impatrq/green_house/documentacion/historias de usuario/historias_de_usuario.docx

HISTORIAS DE USUARIO

1. Como desarrolladores del proyecto, queremos crear un invernadero inteligente para obtener frutas y verduras fuera de temporada.
2. Como cliente, quiero comprar un sistema que se autocontrole y maneje un historial para cultivar y cosechar frutas y verduras, y tener una mejor dieta.
3. Como agricultor, quiero aumentar mi producción fuera de temporada y utilizar menos agroquímicos para aumentar mis ingresos.
4. Como transportista, quiero tener un fácil manejo para el movimiento del invernadero.
5. Como ONG, quiero fomentar el cultivo en invernadero para reducir el consumo de agua.
6. Como nutricionista, quiero que mis clientes tengan una mejor dieta para tener una mejor calidad de vida.
7. Como encargado de supermercado, quiero tener a la venta frutas y verduras frescas fuera de temporada para satisfacer a mis clientes.
8. Como encargado de vivero, quiero mantener a mis plantas sanas y salvas para venderlas en condiciones.
9. Como escuela, quiero enseñar a mis alumnos la importancia del uso del agua para concientizarlos.
10. Como restaurant, quiero ofrecer a mis clientes la misma calidad/cantidad durante todo el año para evitar la compra de frutas congeladas.
11. Como consorcio de edificio, quiero invernaderos en mi terraza para poder recolectar frutas y verdura de manera conjunta.
