impatrq/green_house/Diseños de marca/Stickers/Instagram.pdf

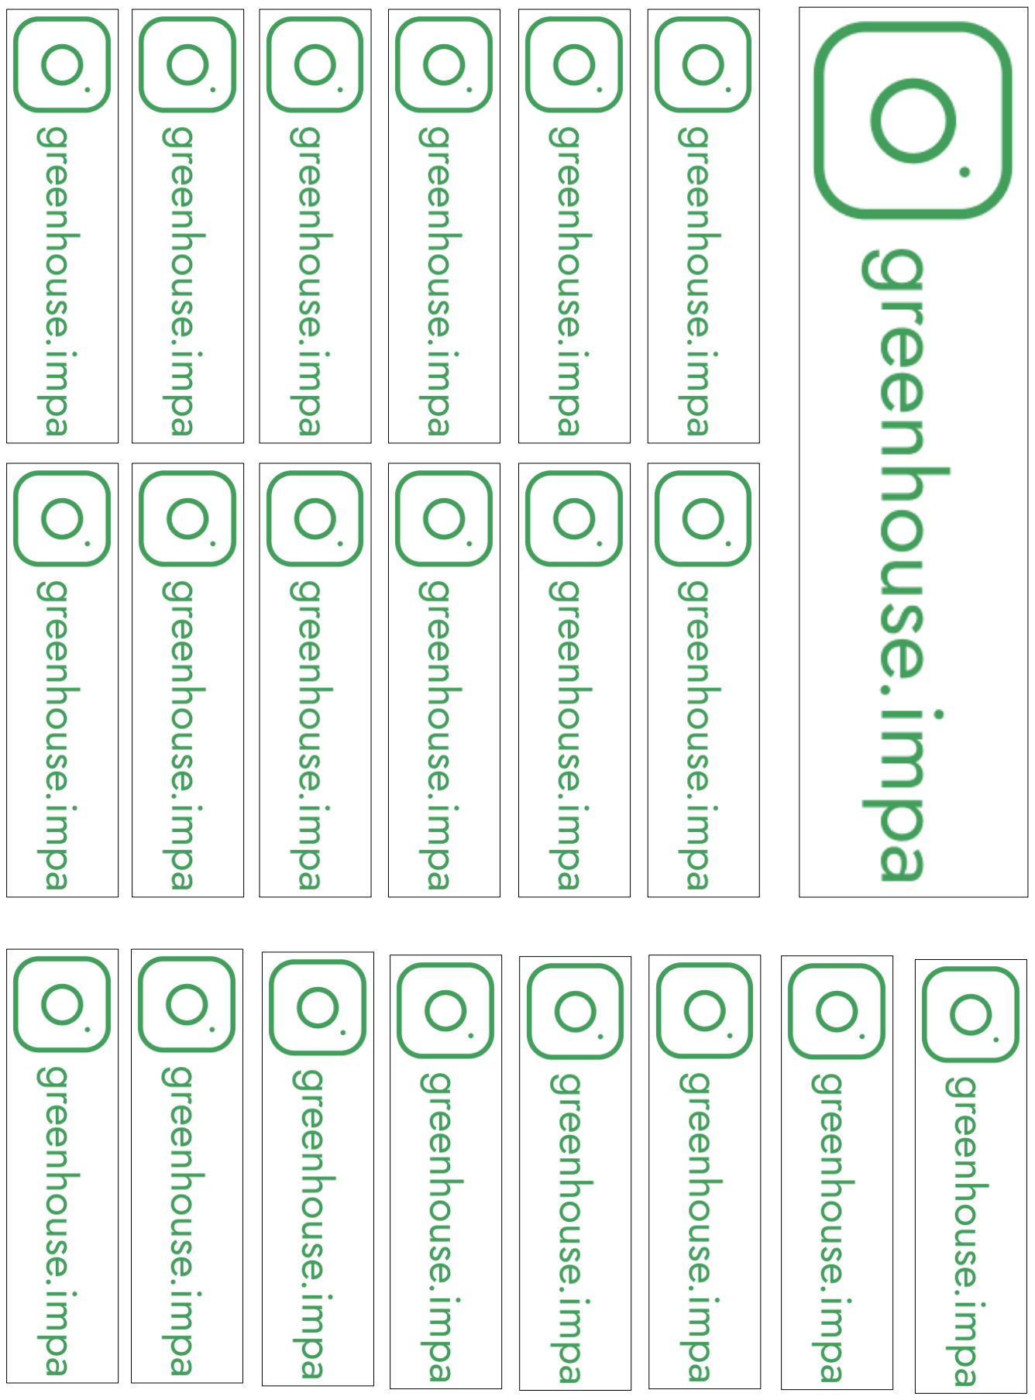
[picture p41: page 1]
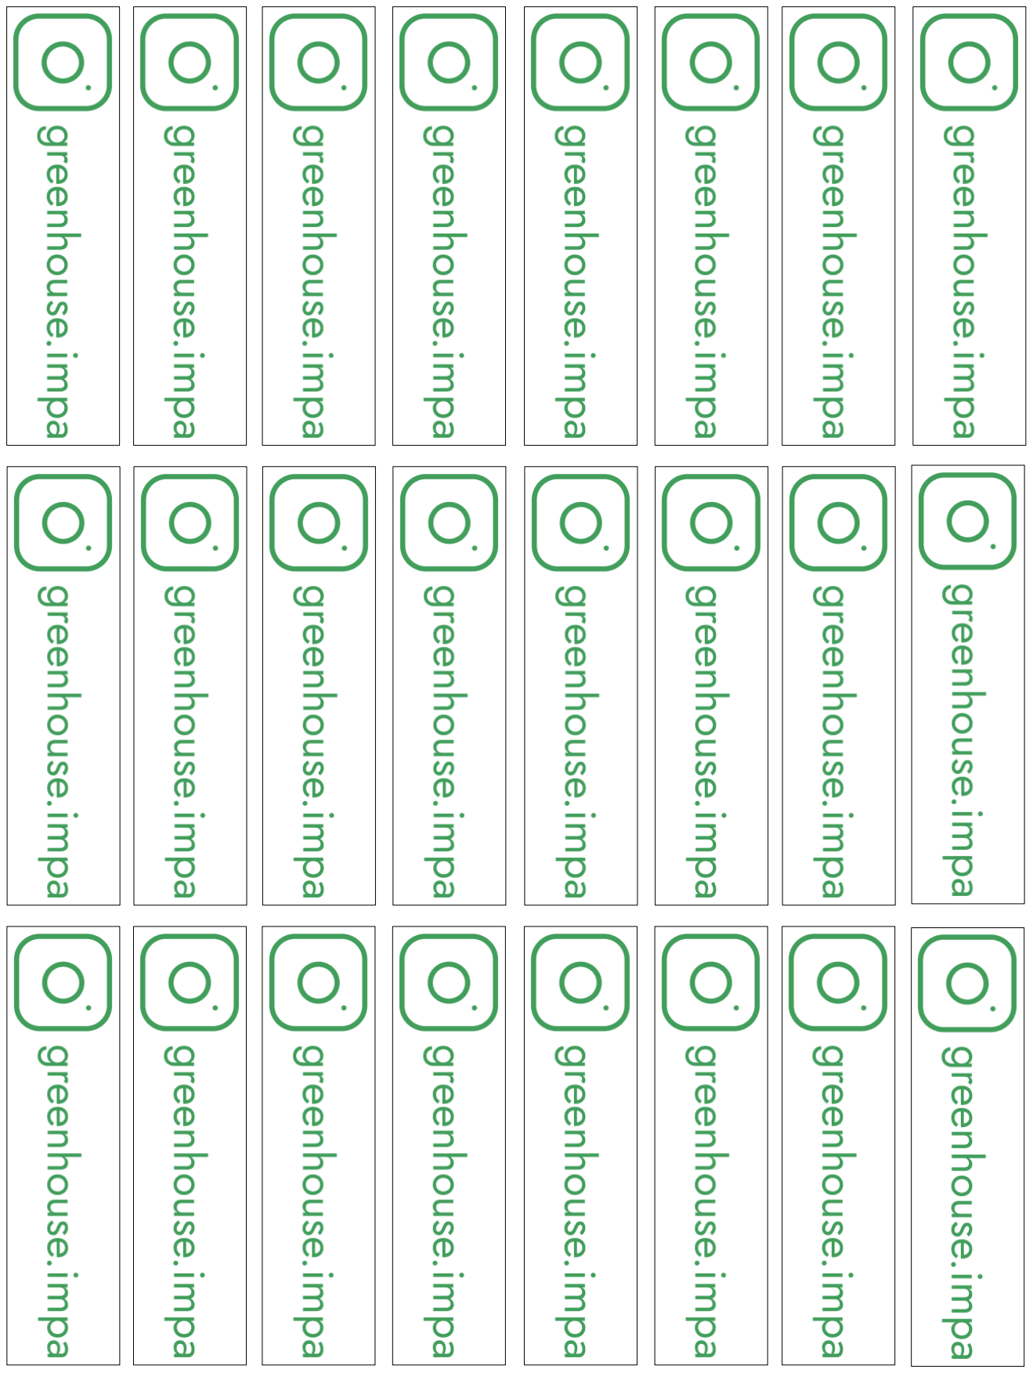
[picture p42: page 2]
