impatrq/green_house/Diseños de marca/Stickers/Nombre y Logo.pdf

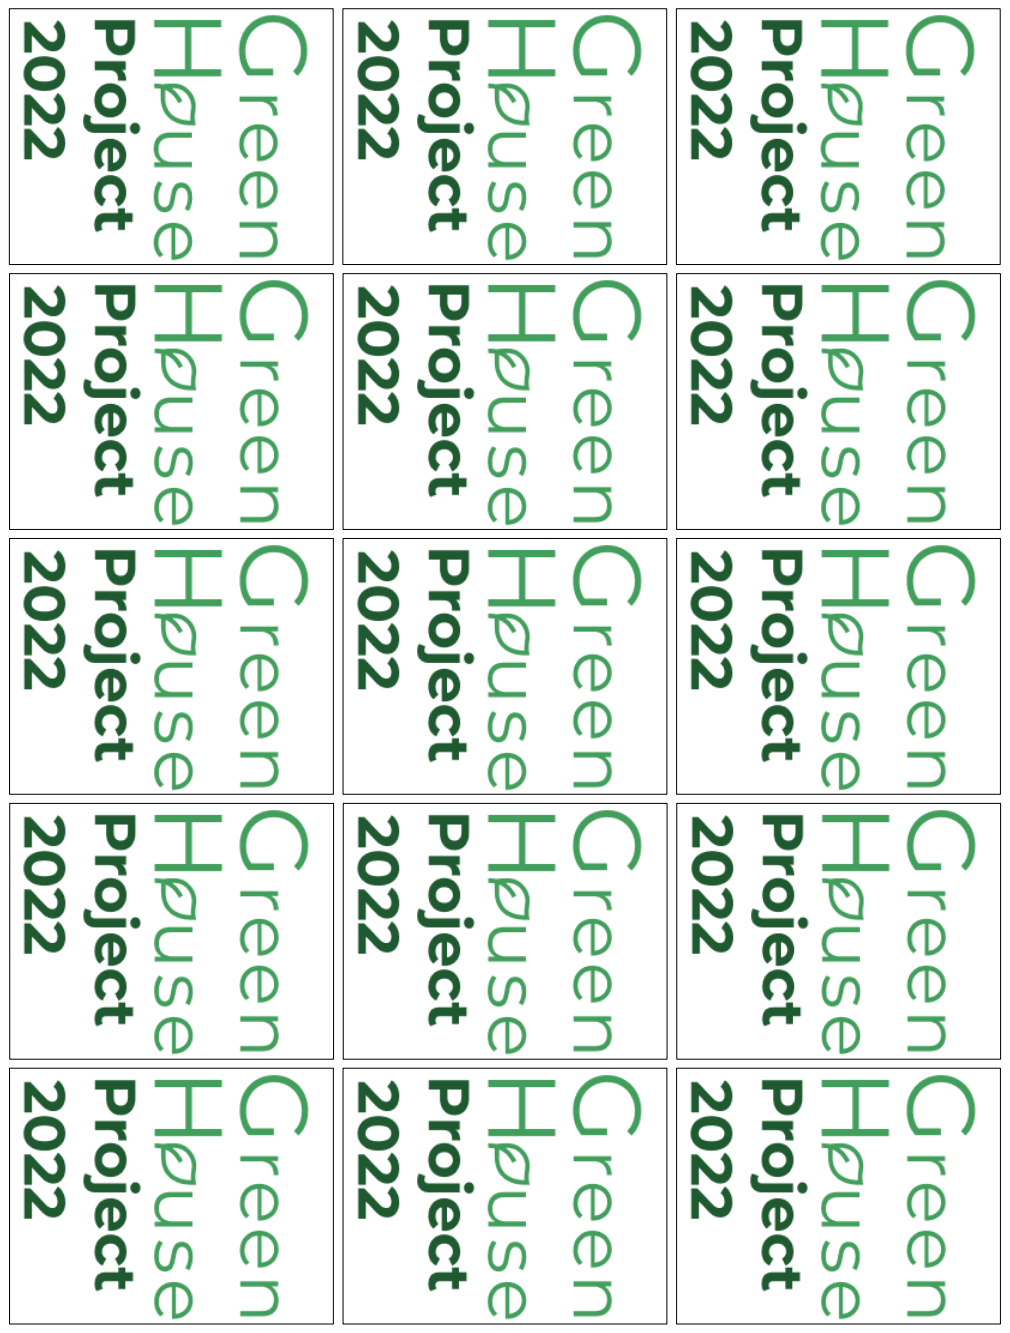
[picture p43: page 1]
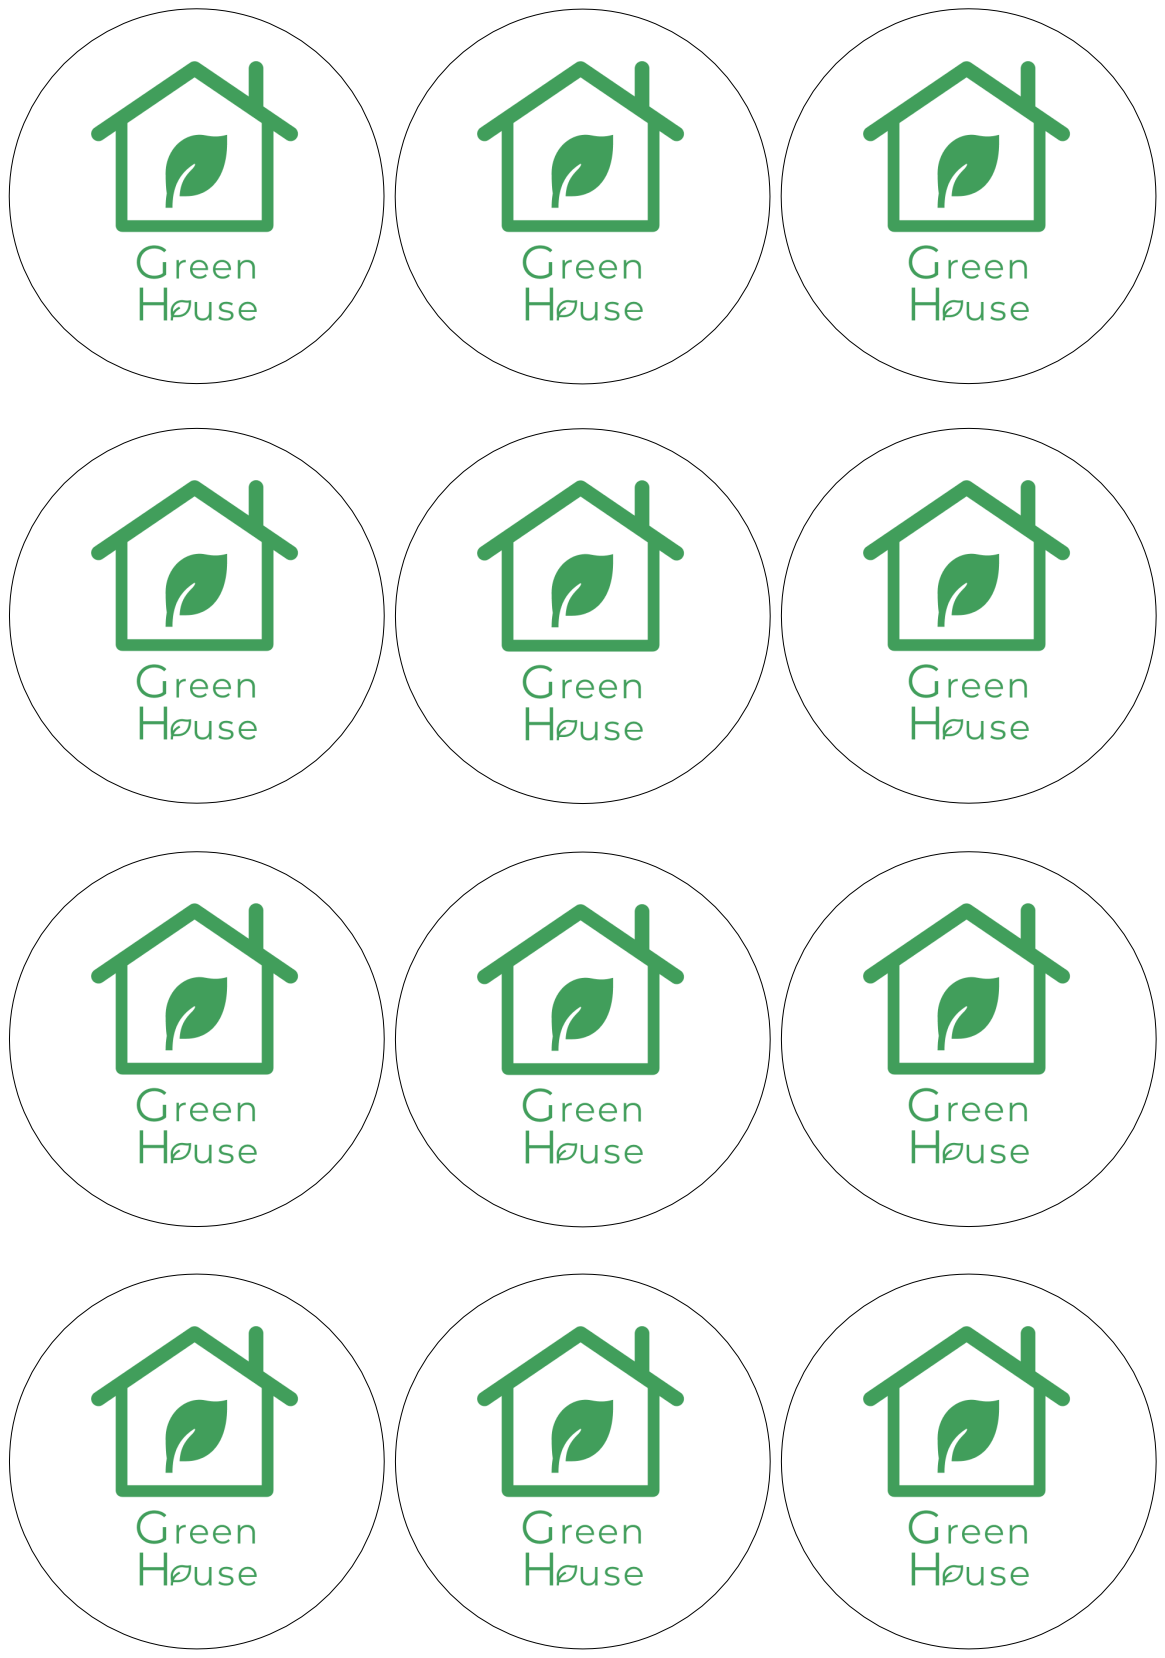
[picture p44: page 3]
