impatrq/green_house/Diseños de marca/Tarjetas de presentacion/Tarjeta de presentacion trasera.pdf

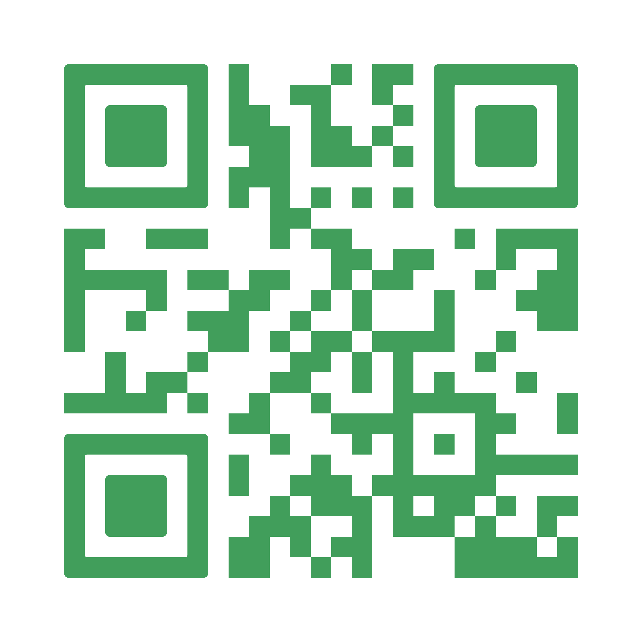
[picture p45: figure]
