impatrq/green_house/documentacion/presentaciones/Presentacion Estilo Venta - GreenHouse.pdf

# ¿Qué es Greenhouse?

GreenHouse es un invernadero automatizado que permite el control de ciertos parámetros como: temperatura y humedad ambiente, luminosidad y humedad de tierra.

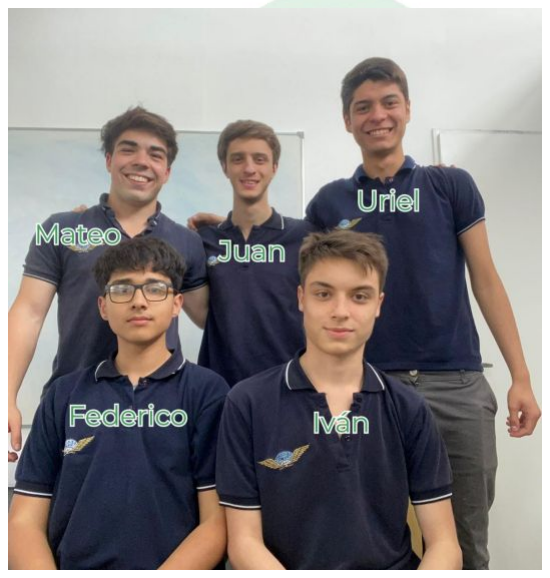
[picture p46: figure]
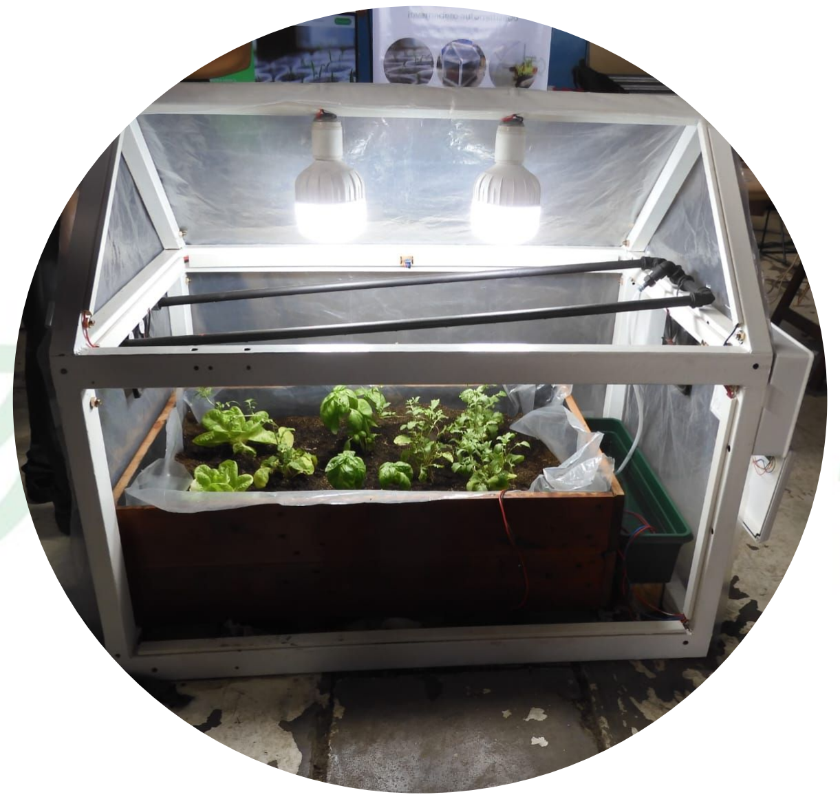
[picture p47: figure]

# ¿A qué apunta Greenhouse?

El objetivo del invernadero es poder darle a nuestros cultivos las condiciones necesarias para desarrollarse, por lo tanto, podemos cultivar plantas que en determinada época no podrían crecer fuera de Greenhouse.
Greenhouse apunta a que cualquier persona que no sepa cómo plantar ni como mantener su cultivo pueda hacerlo sin necesidad de intervenir.

# ¿Por qué adquirir GreenHouse?

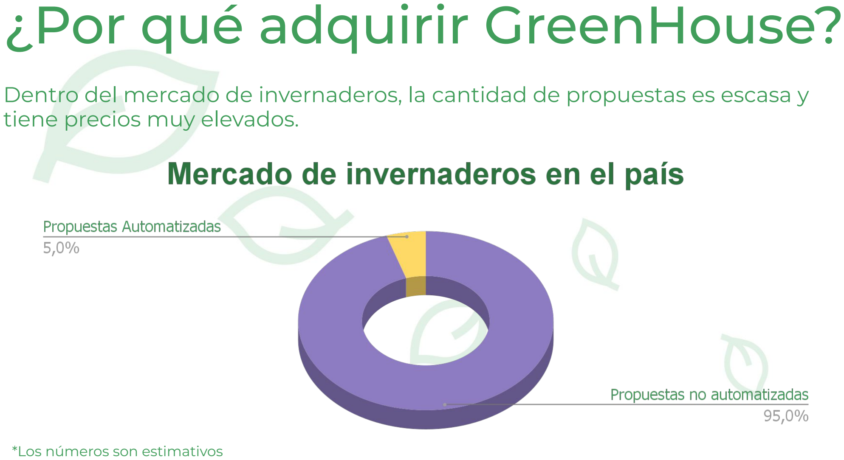
[picture p48: page 4]

Dentro del mercado de invernaderos, la cantidad de propuestas es escasa y tiene precios muy elevados.

*Los números son estimativos

## ¿Podría GreenHouse ingresar al mercado?

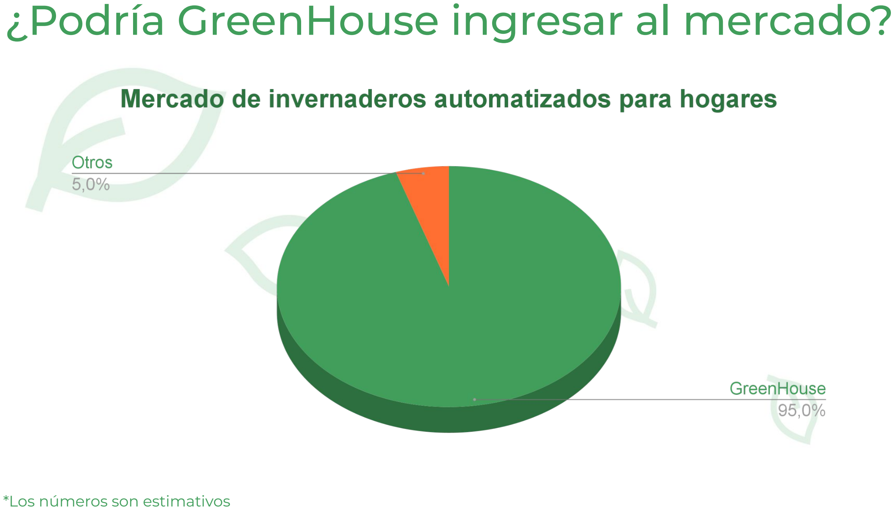
[picture p49: page 5]

*Los números son estimativos

# Ventajas frente a la competencia

### Total automatización

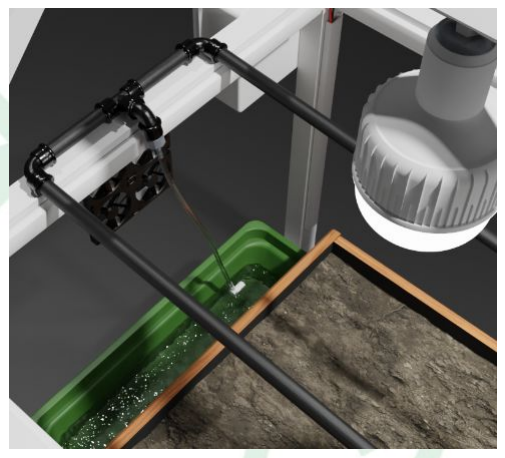
[picture p50: figure]
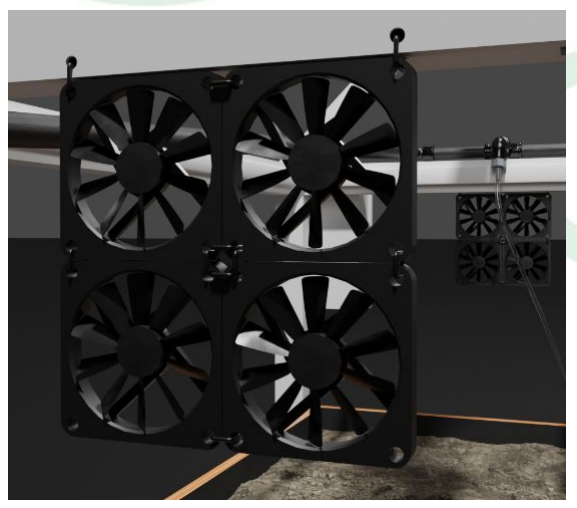
[picture p51: figure]
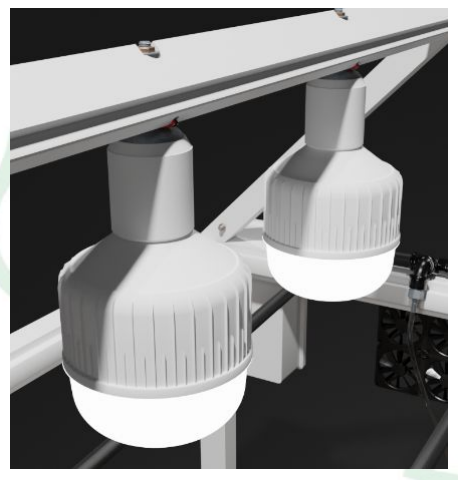
[picture p52: figure]

# Ventajas frente a la competencia

## Interfaz personalizada

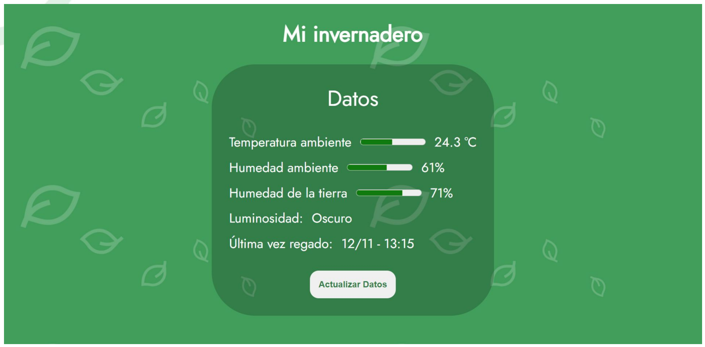
[picture p53: figure]

# Ventajas frente a la competencia

## Relación costo - calidad inmejorable

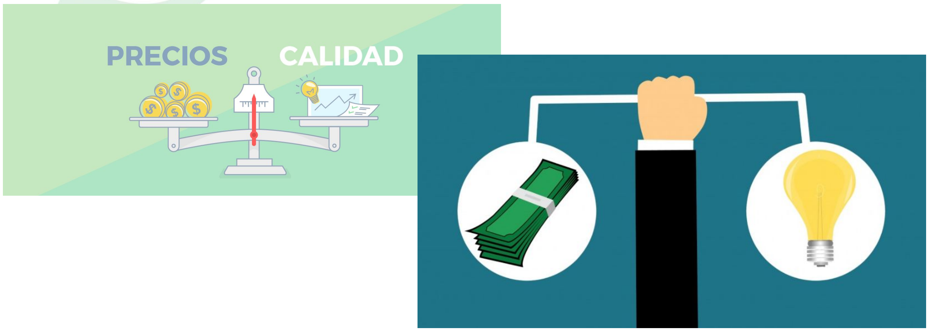
[picture p54: figure]

# Estructura

## Diseño de los planos

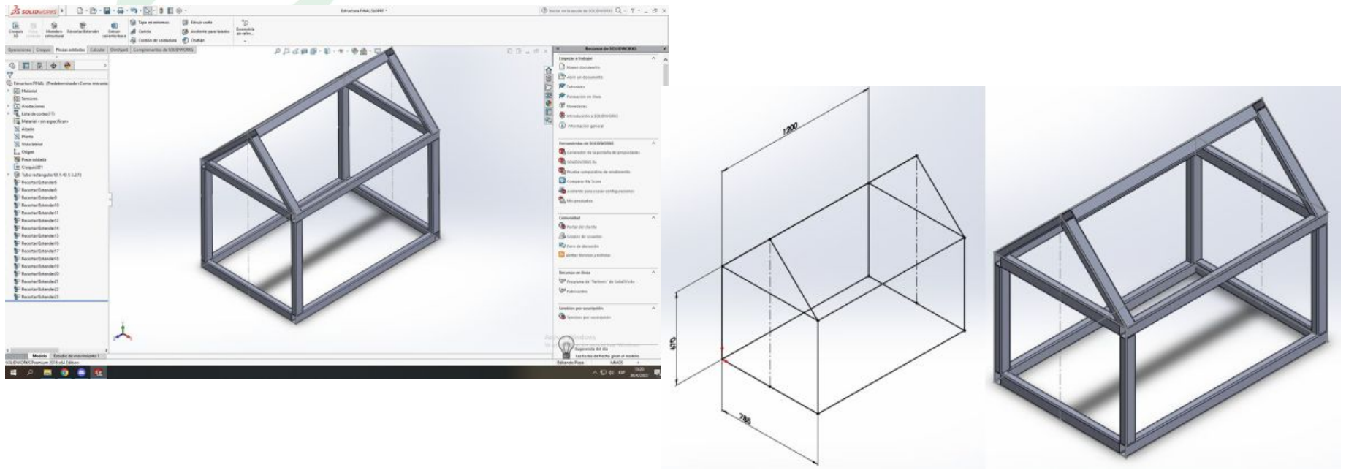
[picture p55: figure]

# Estructura

## Desarrollo

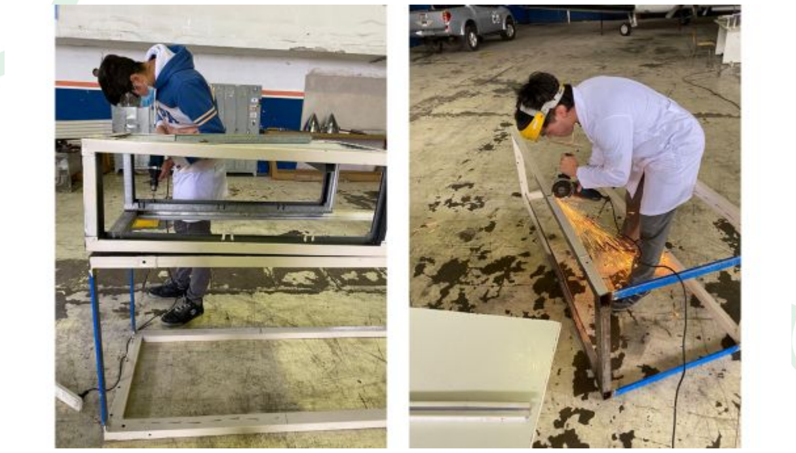
[picture p56: figure]

# Estructura

## Desarrollo

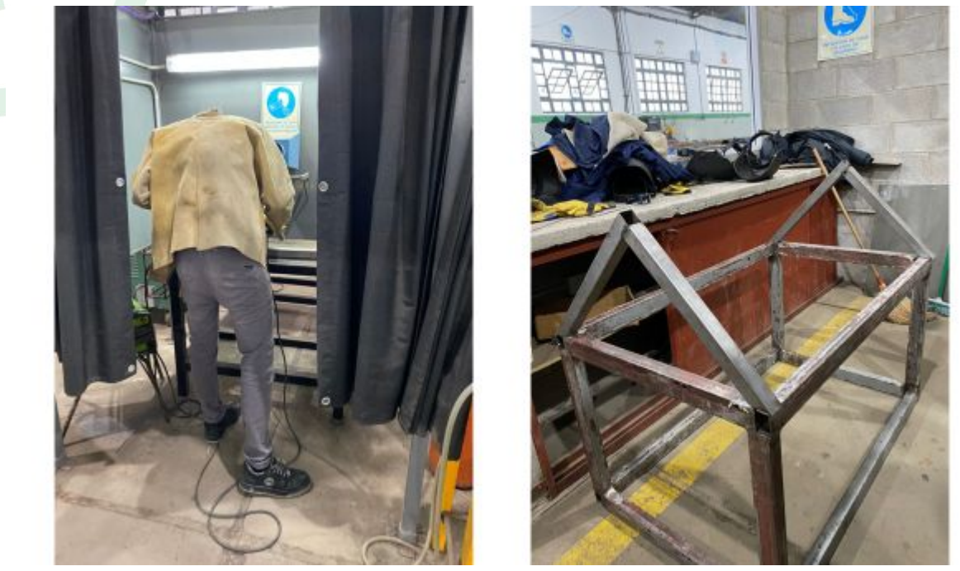
[picture p57: figure]

# Estructura

## Desarrollo

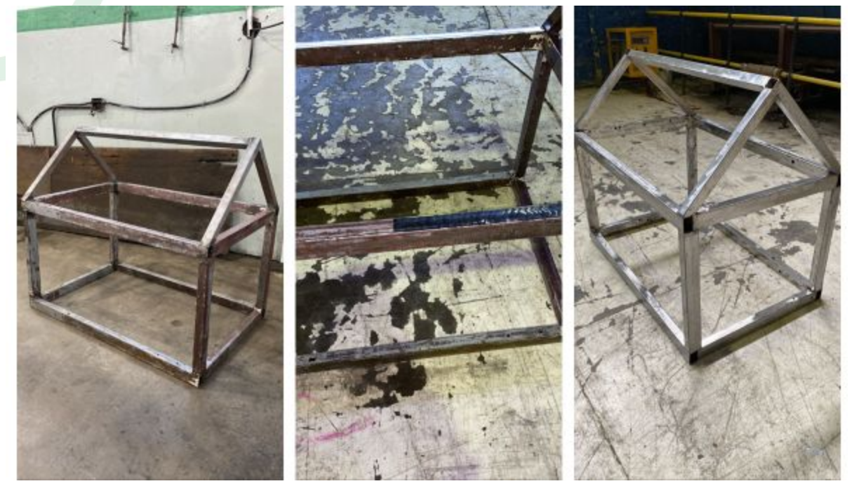
[picture p58: figure]

# Estructura del cajón

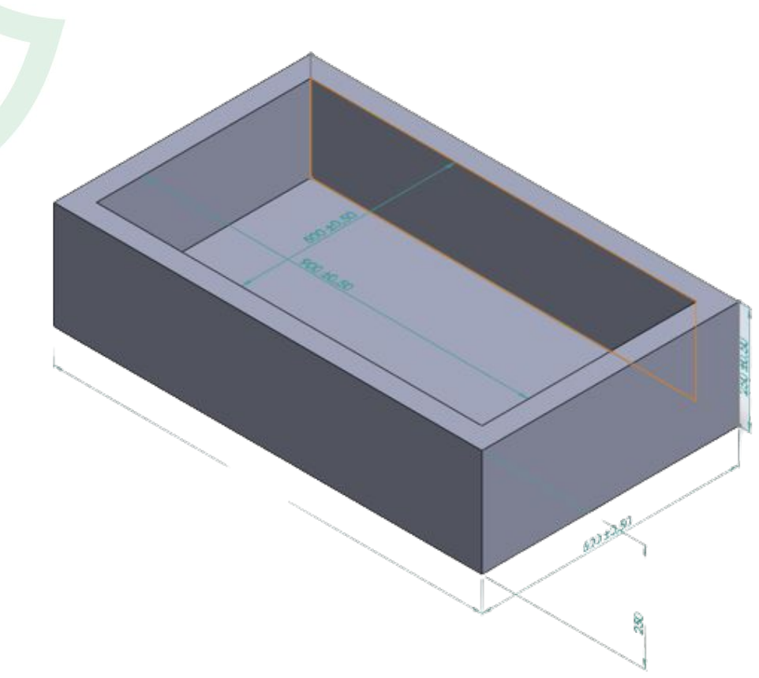
[picture p59: figure]

## Diseño

# Estructura del cajón

## Desarrollo

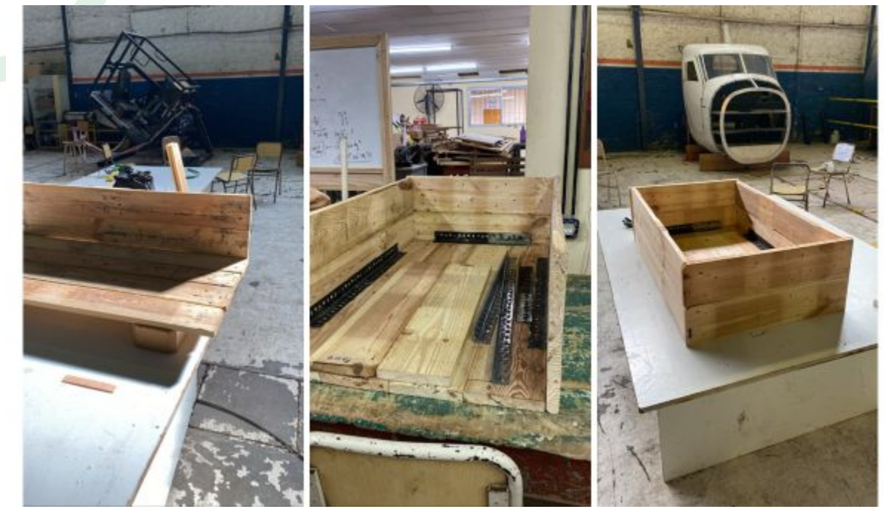
[picture p60: figure]

# Circuito electrónico

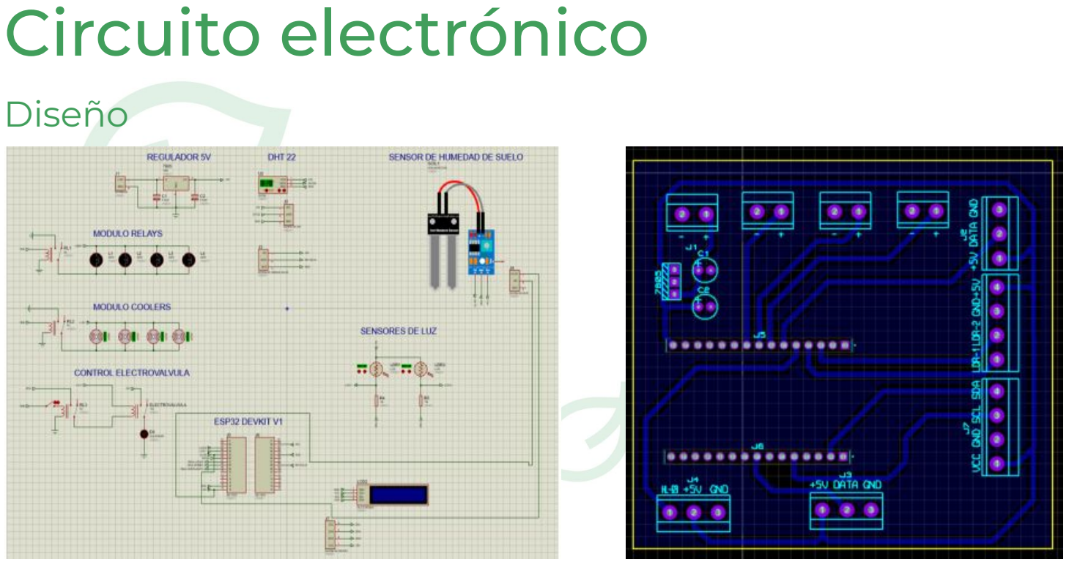
[picture p61: page 15]

Diseño

# Circuito electrónico

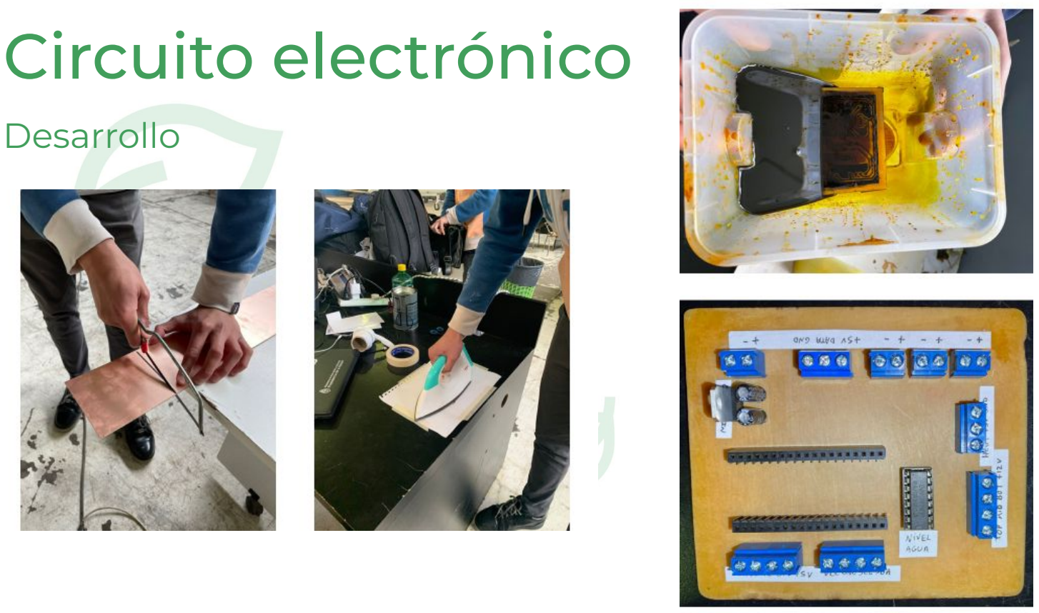
[picture p62: page 16]

Desarrollo

# Funcionamiento de hardware

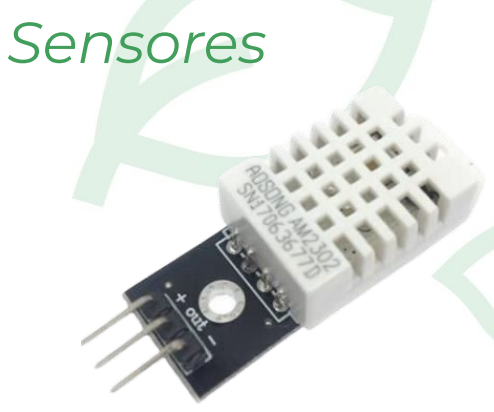
[picture p63: figure]
Sensores
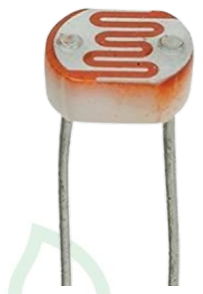
[picture p64: figure]
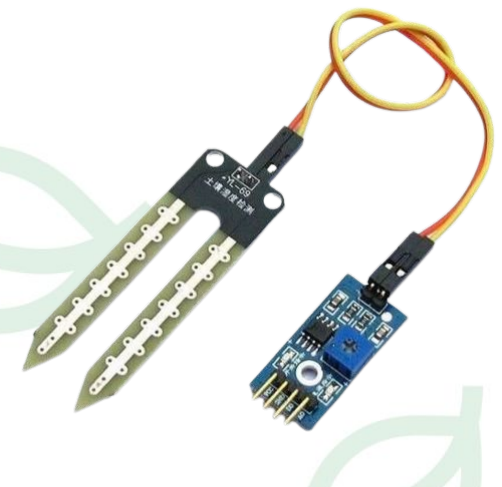
[picture p65: figure]
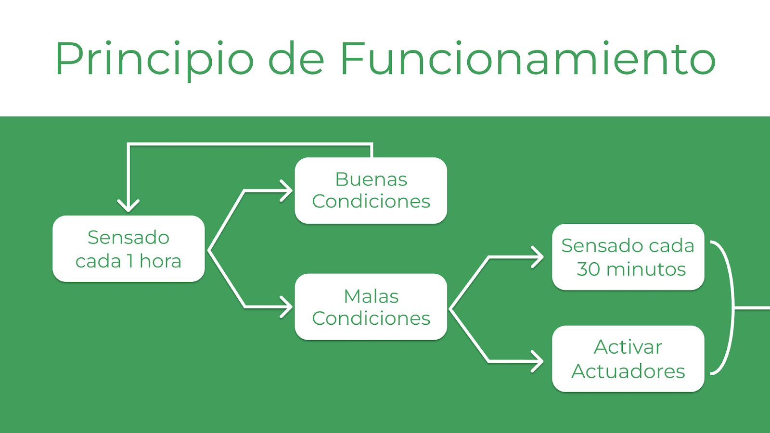
[picture p66: page 18]
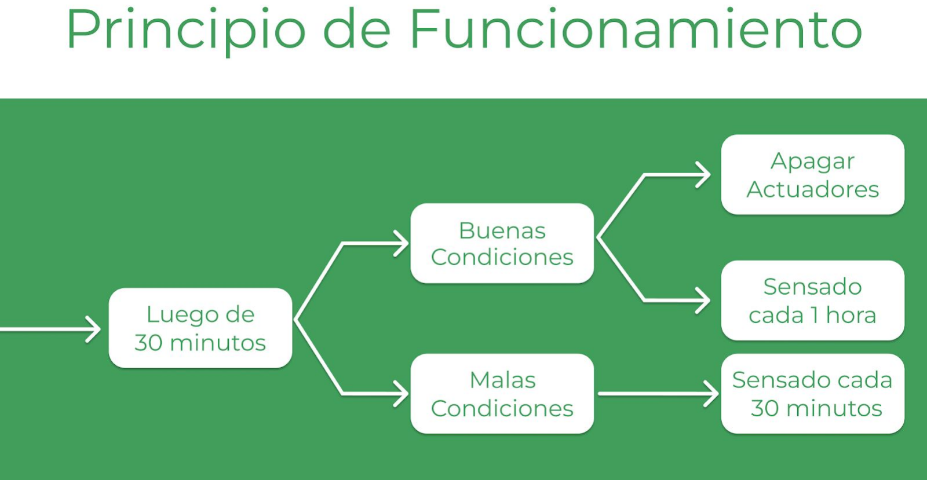
[picture p67: page 19]

# Diseño 3D

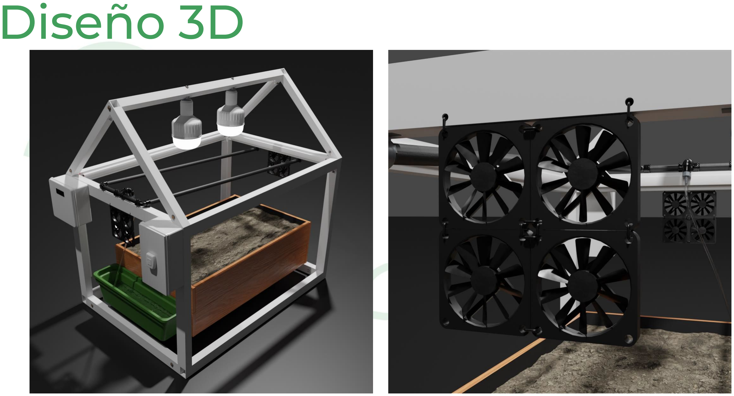
[picture p68: page 20]

# Diseño 3D

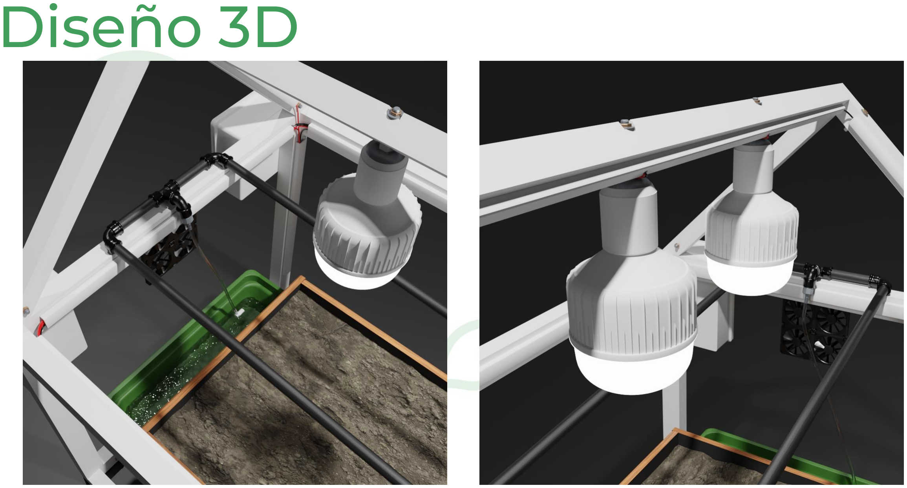
[picture p69: page 21]

# Diseño 3D

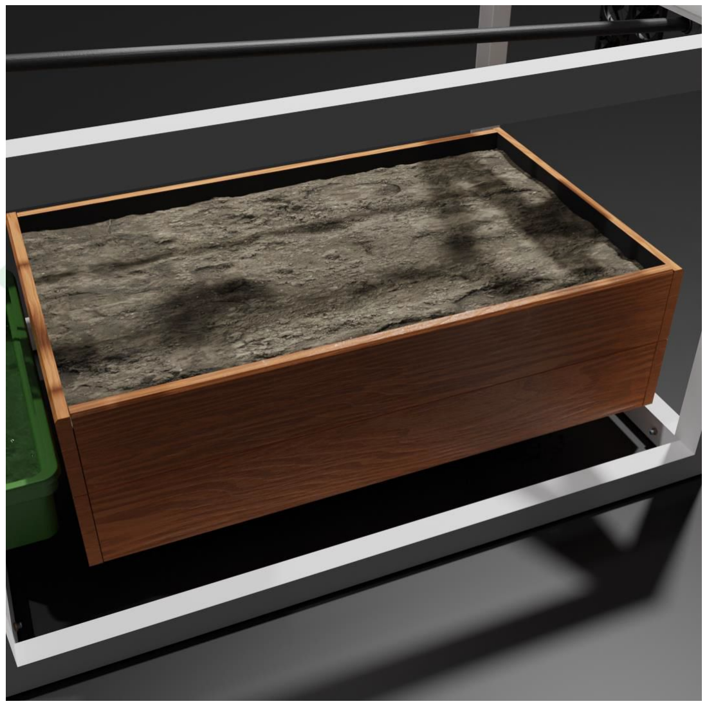
[picture p70: figure]

# Página web

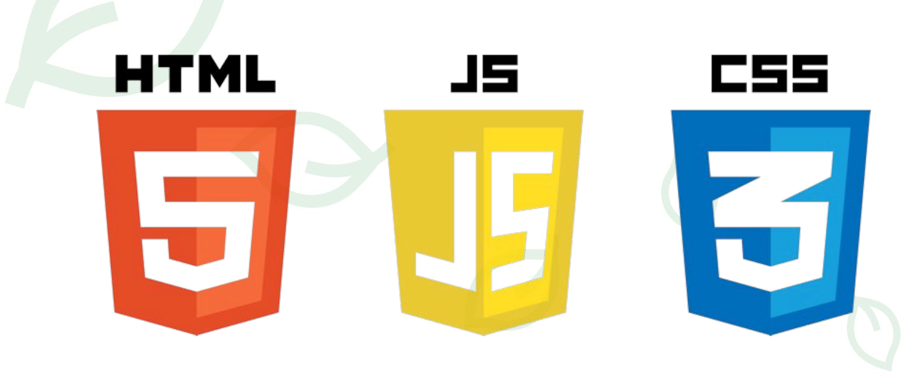
[picture p71: figure]

# Página web

Desarrollo

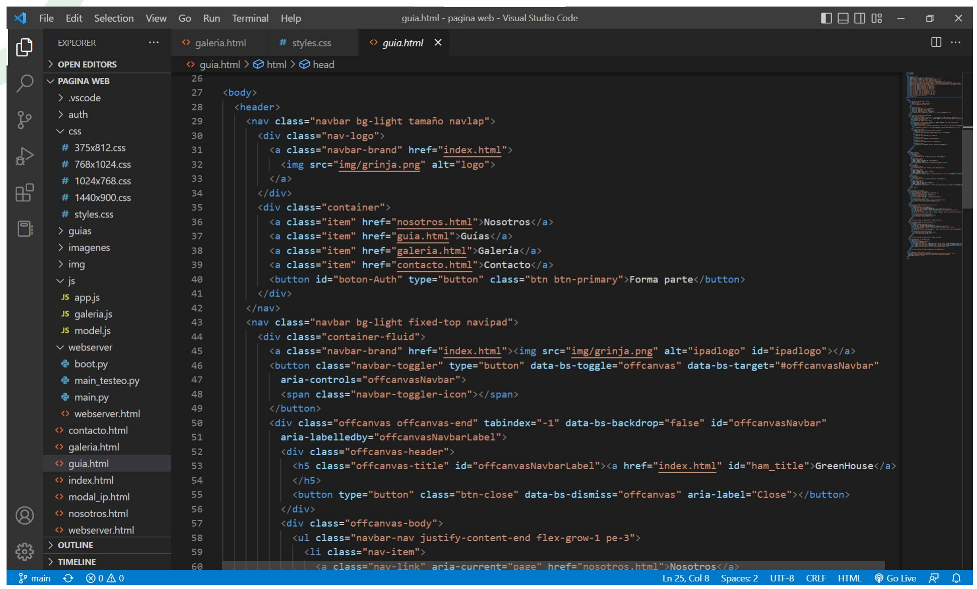
[picture p72: figure]

# Página web

Resultado

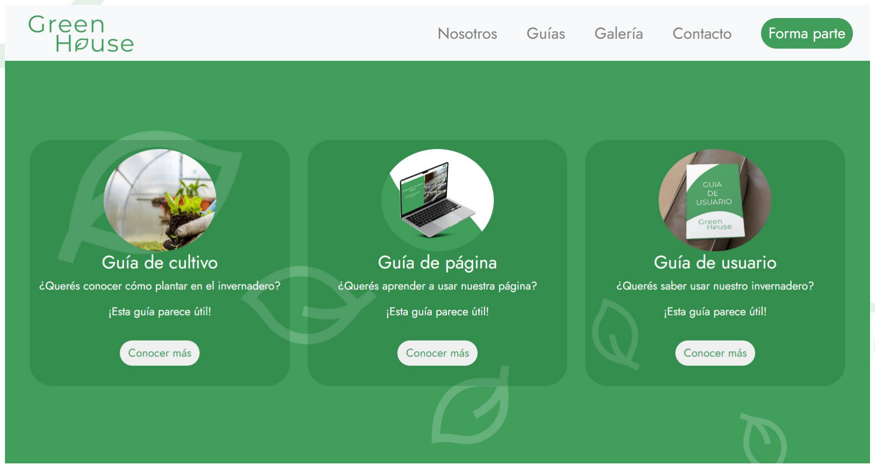
[picture p73: figure]
