impatrq/green_house/pagina web/img/Background_Guias.png

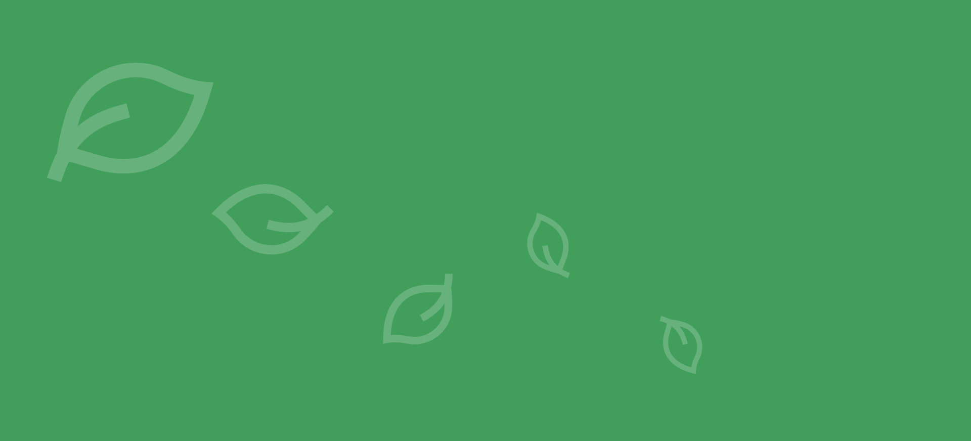
pagina web/img/Background_Guias.png
