impatrq/green_house/pagina web/img/fede.png

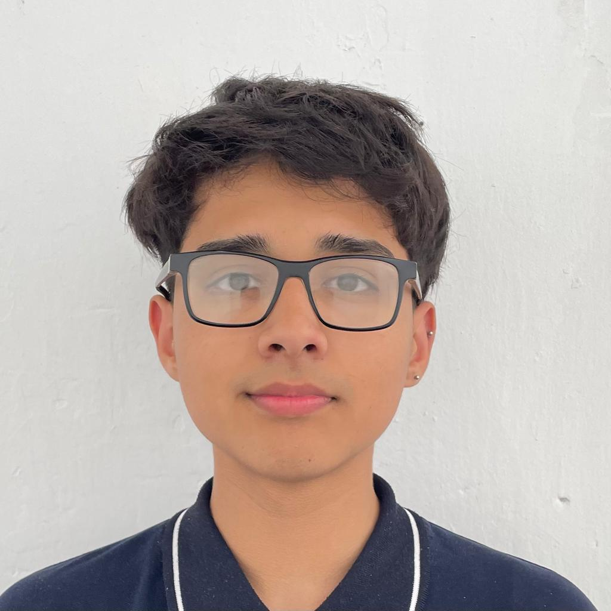
pagina web/img/fede.png
