impatrq/green_house/pagina web/img/grinja.png

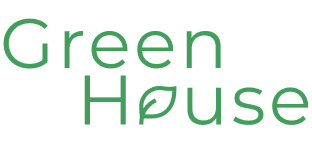
pagina web/img/grinja.png
