impatrq/green_house/pagina web/img/guia_pagina.png

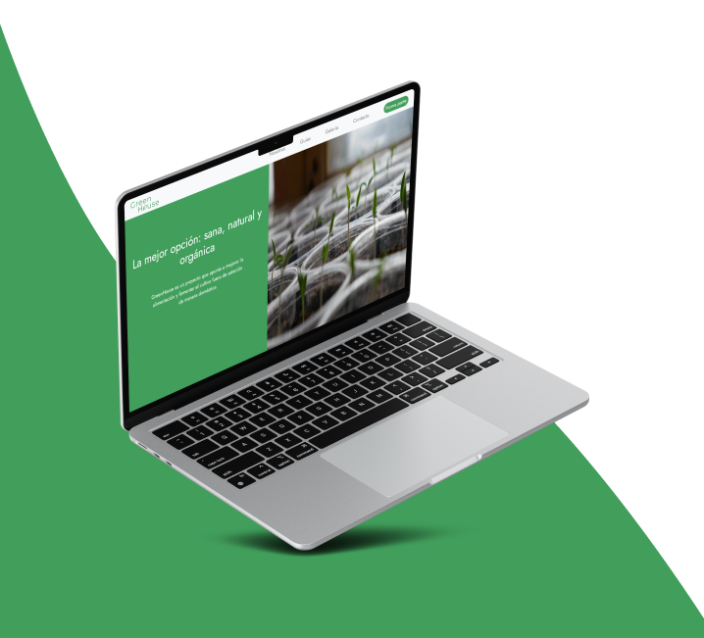
pagina web/img/guia_pagina.png
