impatrq/green_house/pagina web/img/ivan.jpg

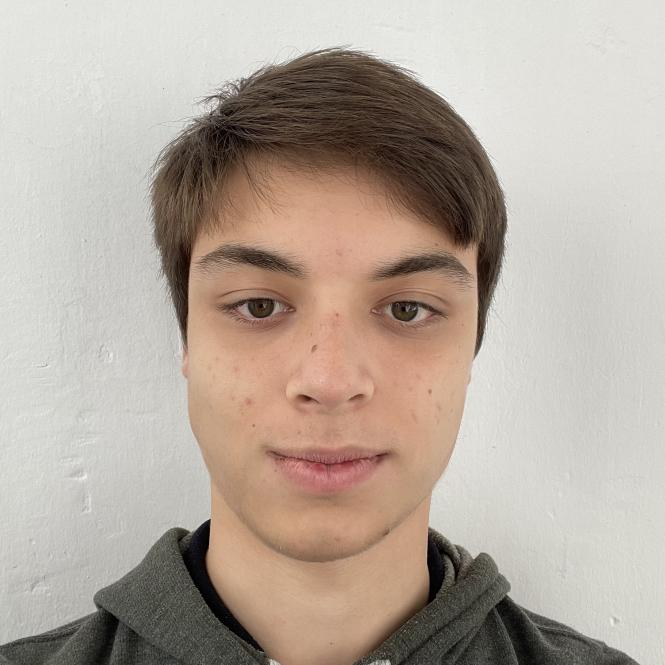
pagina web/img/ivan.jpg
