impatrq/green_house/pagina web/img/juan.jpg

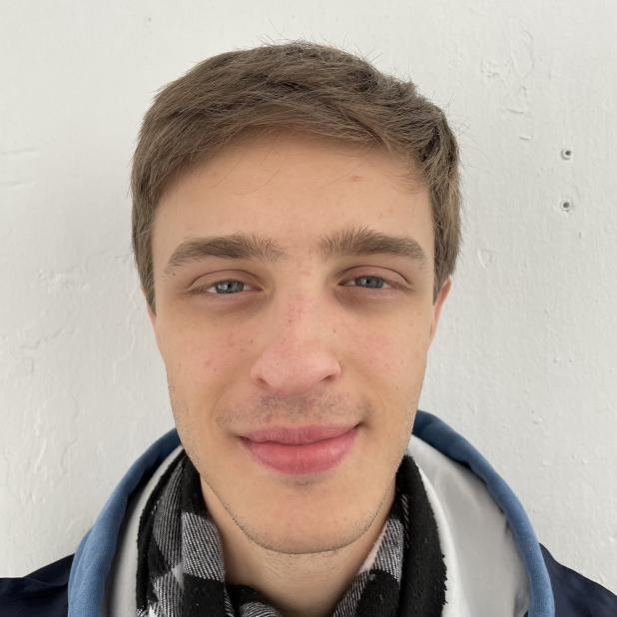
pagina web/img/juan.jpg
