impatrq/green_house/pagina web/img/mateo.jpg

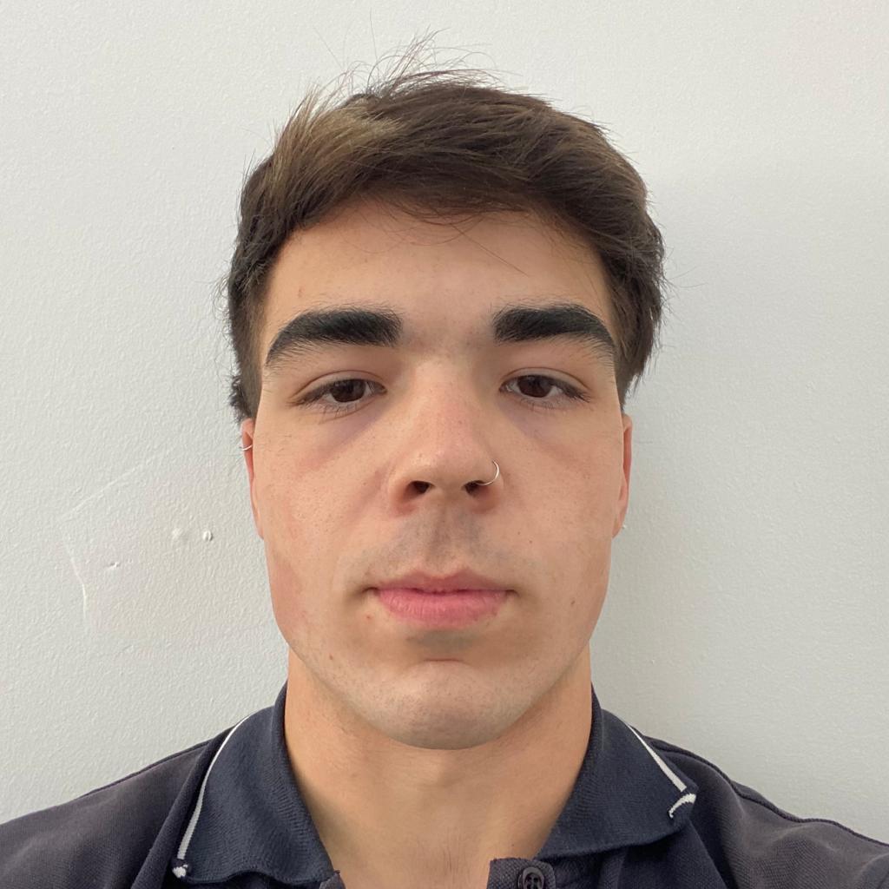
pagina web/img/mateo.jpg
