impatrq/green_house/pagina web/img/momo.PNG

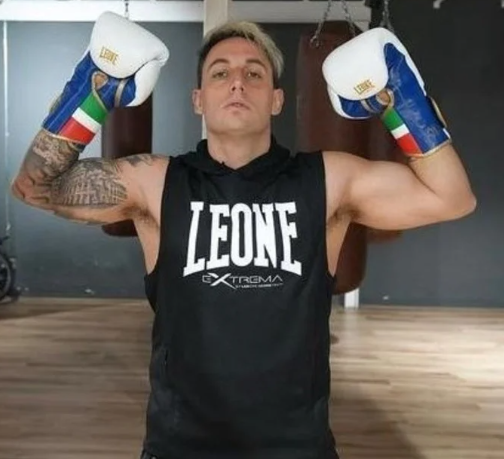
pagina web/img/momo.PNG
