impatrq/green_house/pagina web/img/proceso 1.jpeg

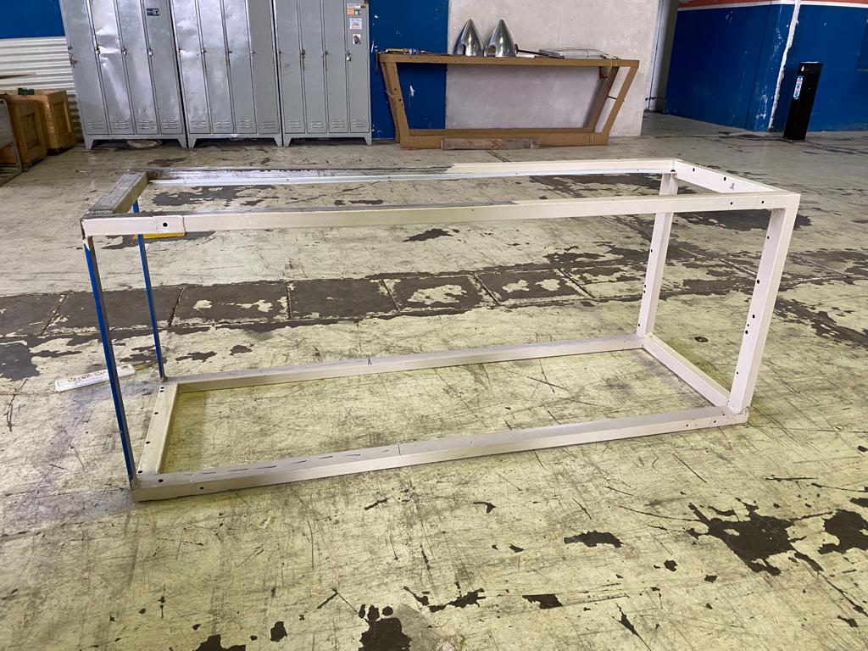
pagina web/img/proceso 1.jpeg
