impatrq/green_house/pagina web/img/proceso 2.jpeg

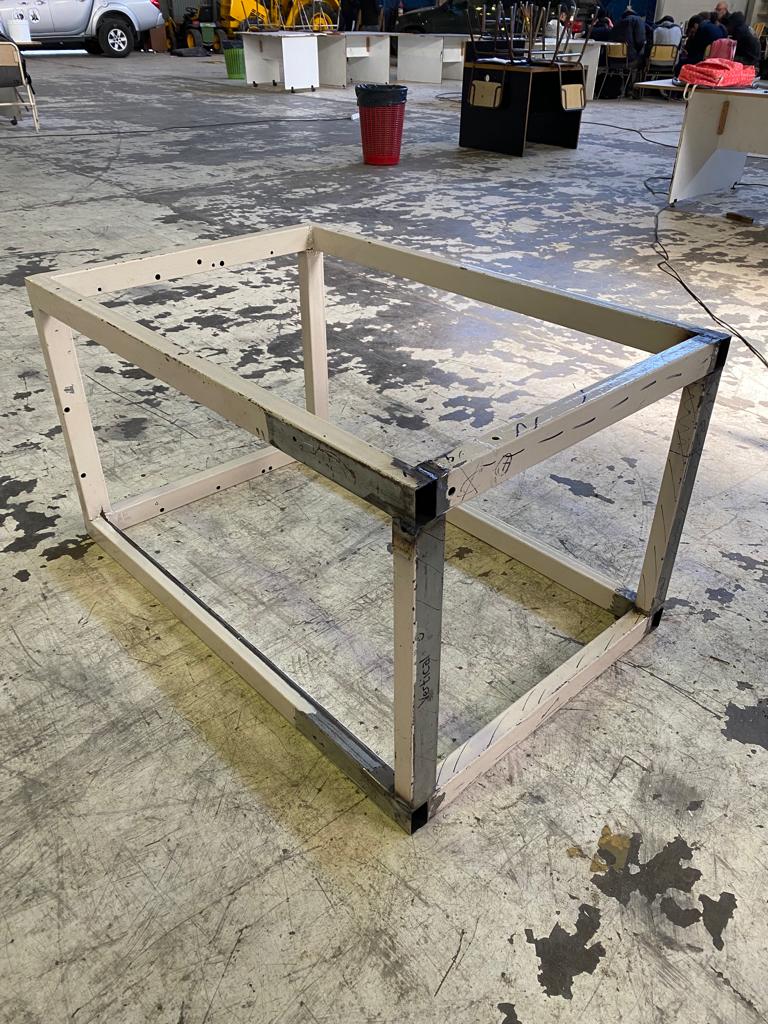
pagina web/img/proceso 2.jpeg
