impatrq/green_house/pagina web/img/proceso 3.jpeg

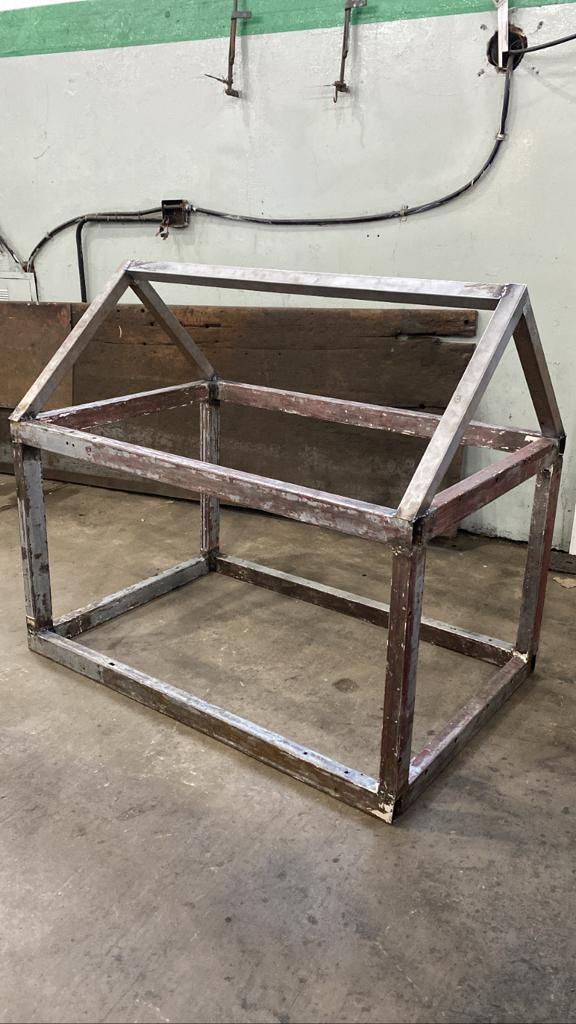
pagina web/img/proceso 3.jpeg
