impatrq/green_house/pagina web/img/proceso 4.jpeg

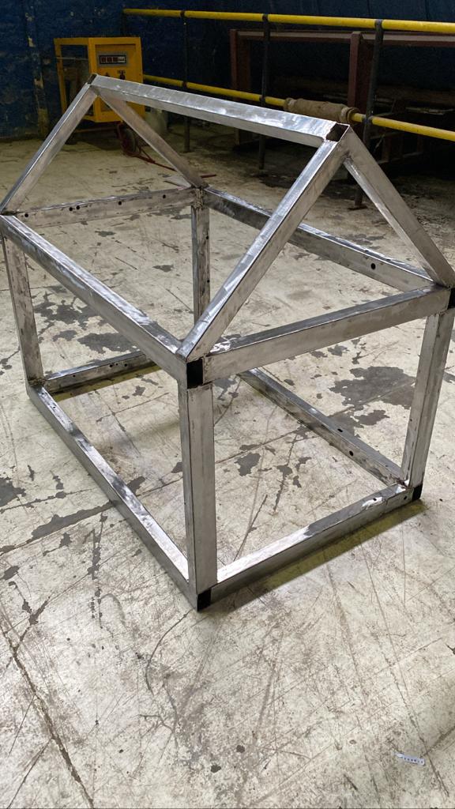
pagina web/img/proceso 4.jpeg
