impatrq/green_house/pagina web/img/proceso 5.jpeg

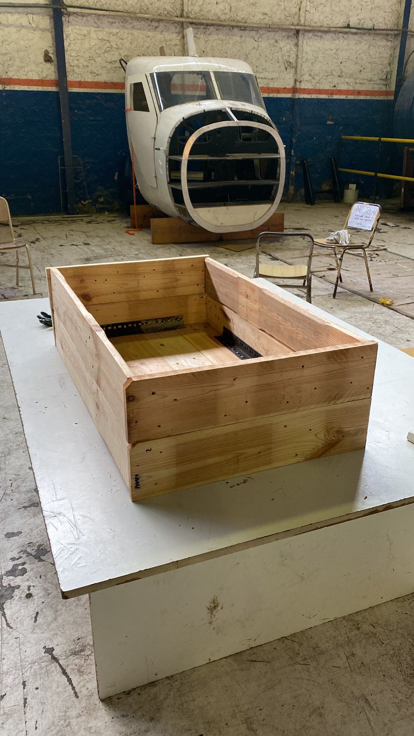
pagina web/img/proceso 5.jpeg
