impatrq/green_house/pagina web/img/proceso 6.jpeg

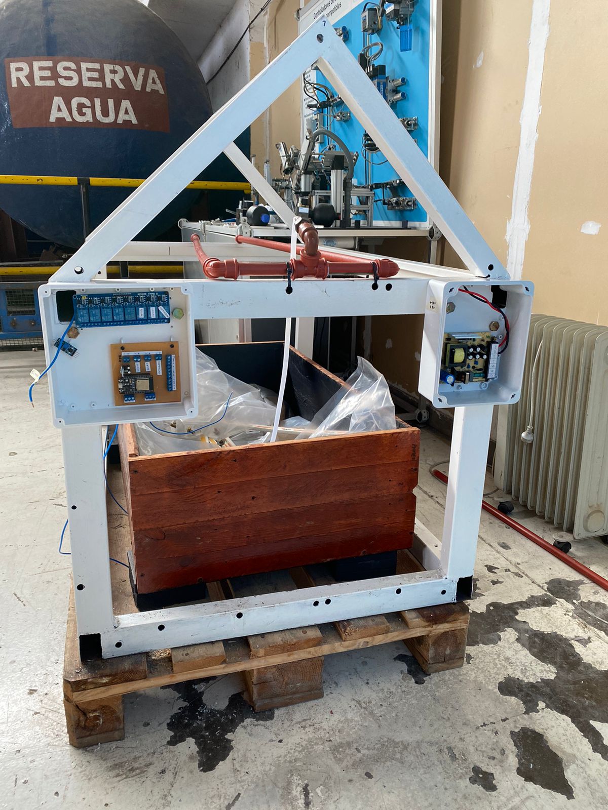
pagina web/img/proceso 6.jpeg
