impatrq/green_house/pagina web/img/proceso 7.jpeg

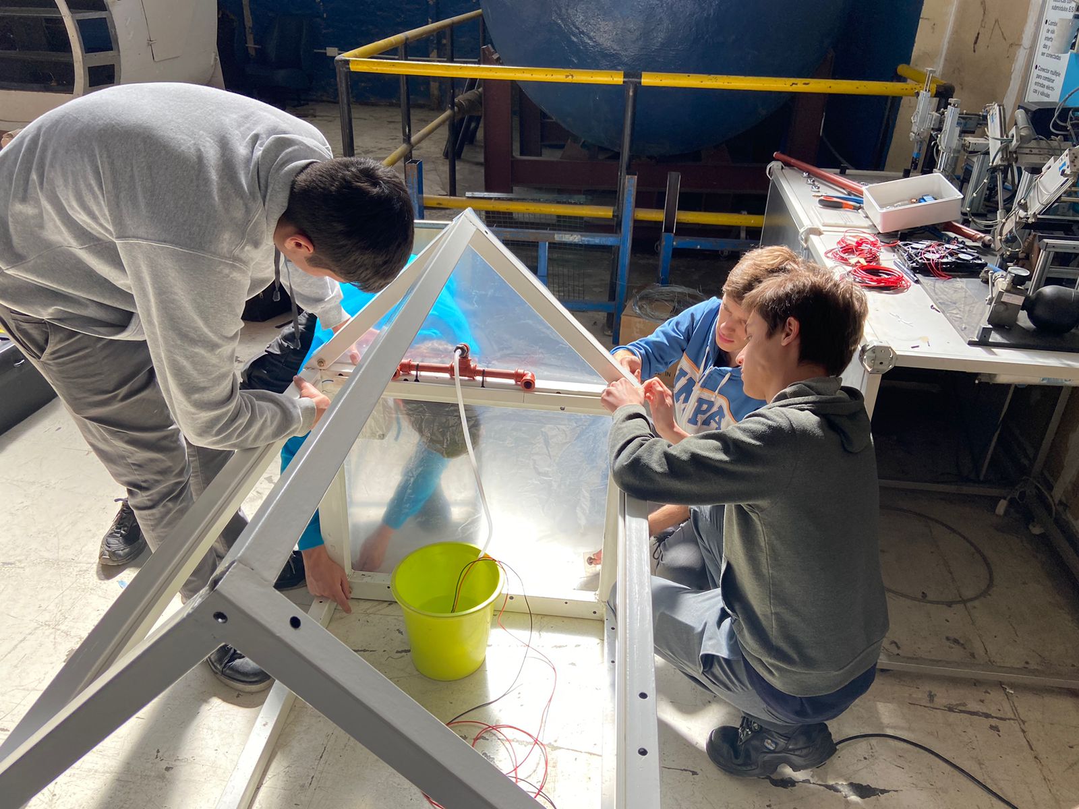
pagina web/img/proceso 7.jpeg
