impatrq/green_house/pagina web/img/proceso 8.jpeg

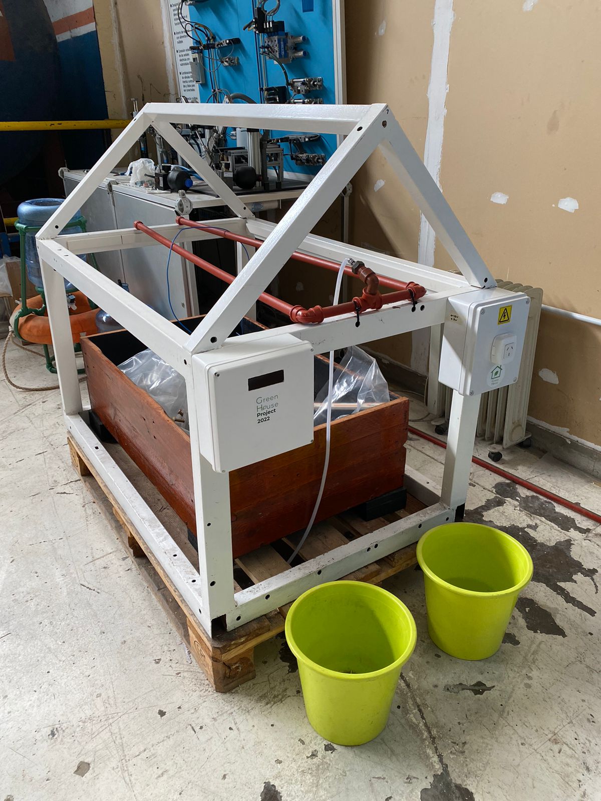
pagina web/img/proceso 8.jpeg
