impatrq/green_house/pagina web/img/proceso 9.jpg

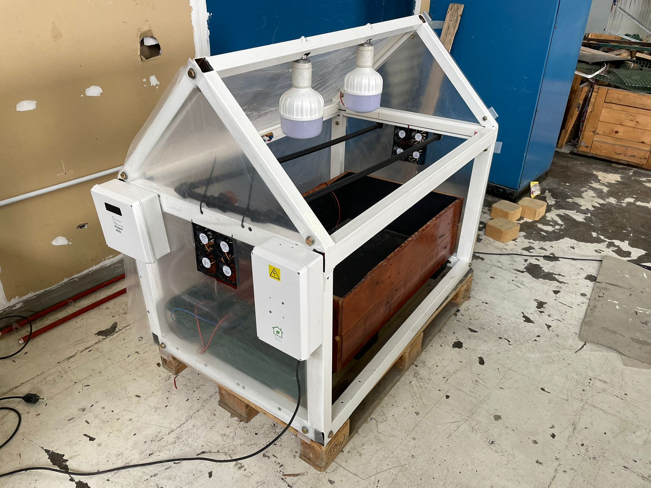
pagina web/img/proceso 9.jpg
