impatrq/green_house/pagina web/img/uriel.jpg

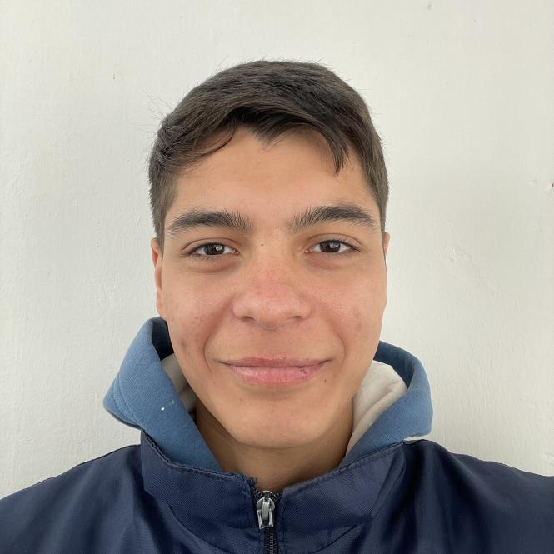
pagina web/img/uriel.jpg
