impatrq/green_house/Proteus/Esquematico.png

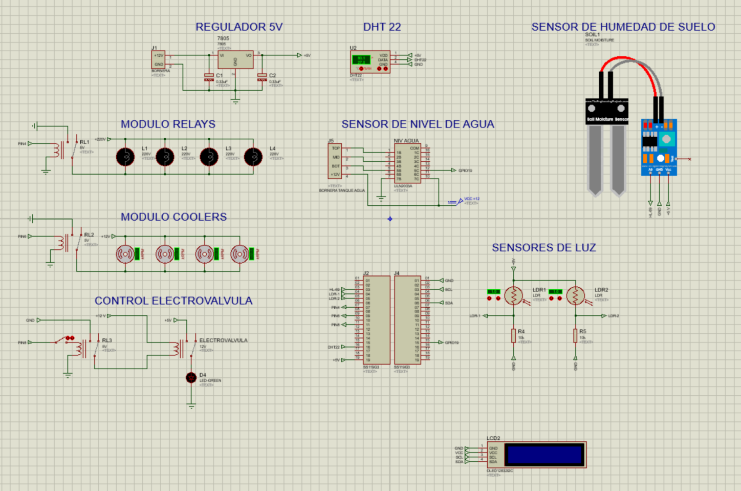
Proteus/Esquematico.png
