impatrq/green_house/Proteus/PCB layout.png

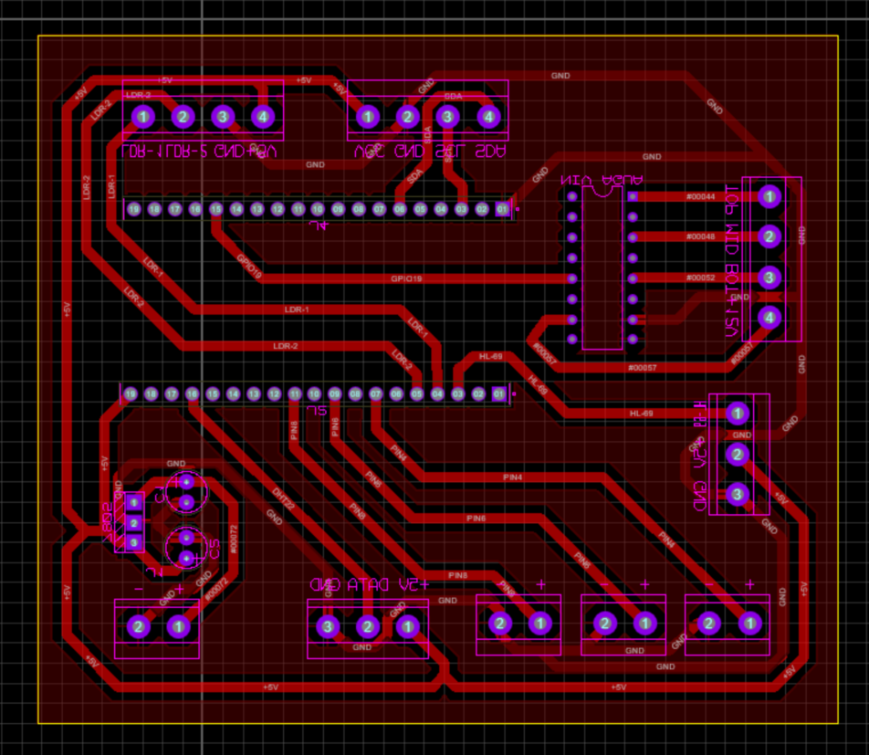
Proteus/PCB layout.png
