impatrq/green_house/Proteus/PCB frontal con componentes.png

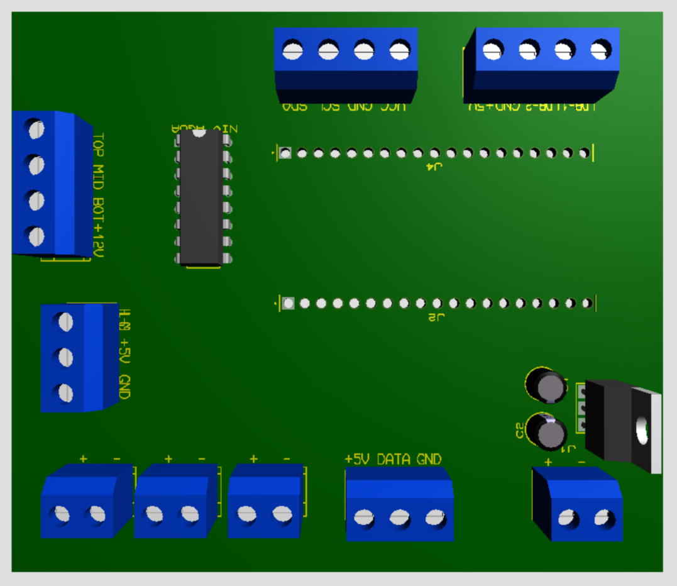
Proteus/PCB frontal con componentes.png
