impatrq/green_house/Proteus/PCB frontal sin componentes.png

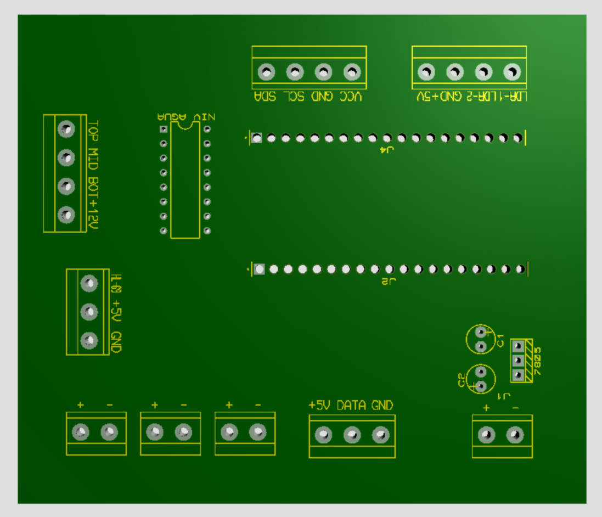
Proteus/PCB frontal sin componentes.png
