impatrq/green_house/Proteus/PCB lateral con componentes.png

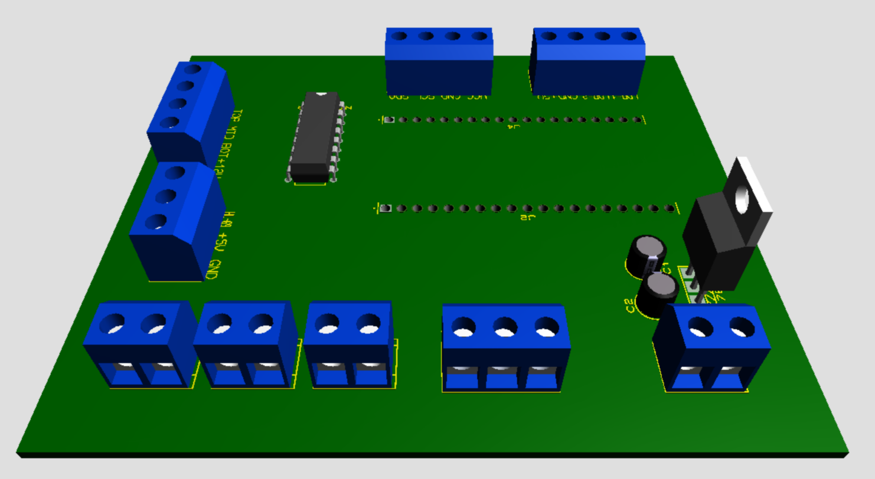
Proteus/PCB lateral con componentes.png
