impatrq/green_house/Proteus/PCB lateral sin componentes.png

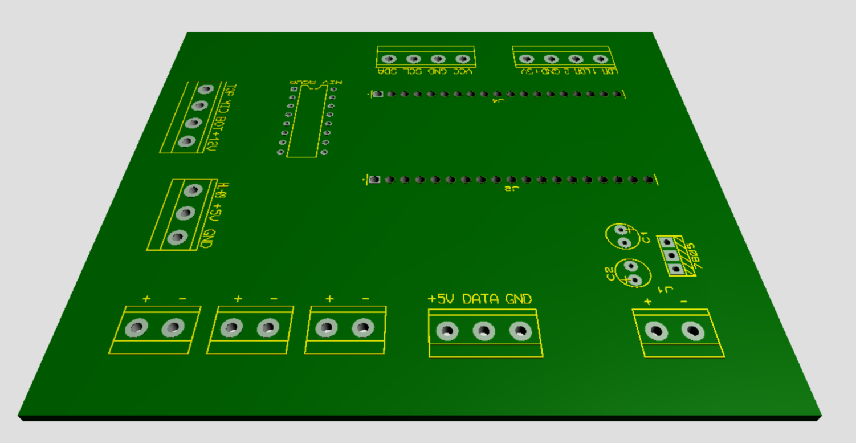
Proteus/PCB lateral sin componentes.png
