impatrq/green_house/Proteus/PCB trasera sin componentes.png

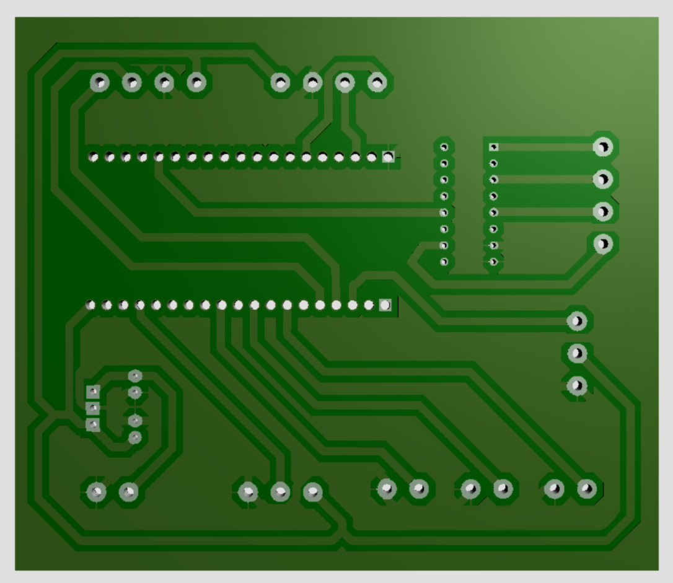
Proteus/PCB trasera sin componentes.png
