impatrq/green_house/SolidWorks/Estructura con medidas.PDF

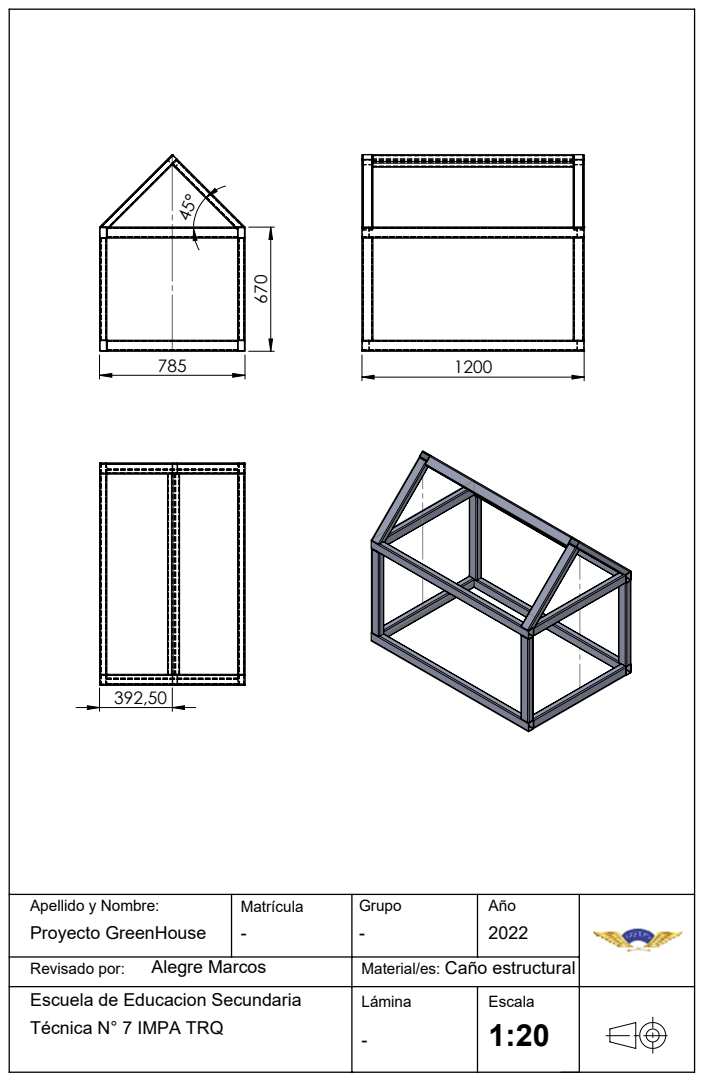
[picture p115: page 1]

Apellido y Nombre: Proyecto GreenHouse | Matrícula - - | Grupo | Año 2022

Alegre Marcos Revisado por: | | Caño estructural Material/es:
Escuela de Educacion Secundaria Técnica N° 7 IMPA TRQ | Lámina - | Escala 1:20
