impatrq/green_house/Proteus/PCB espejada horizontal.PDF

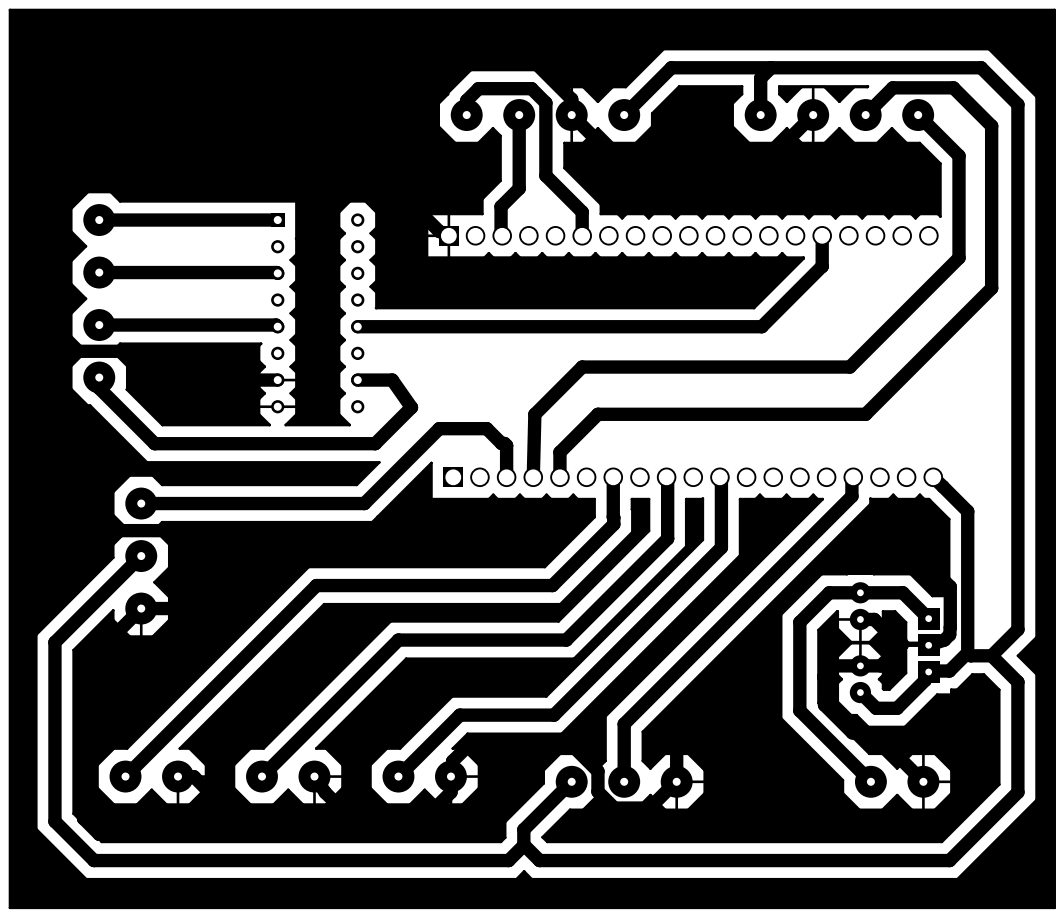
[picture p121: page 1]
