impatrq/green_house/Proteus/PCB espejada vertical.PDF

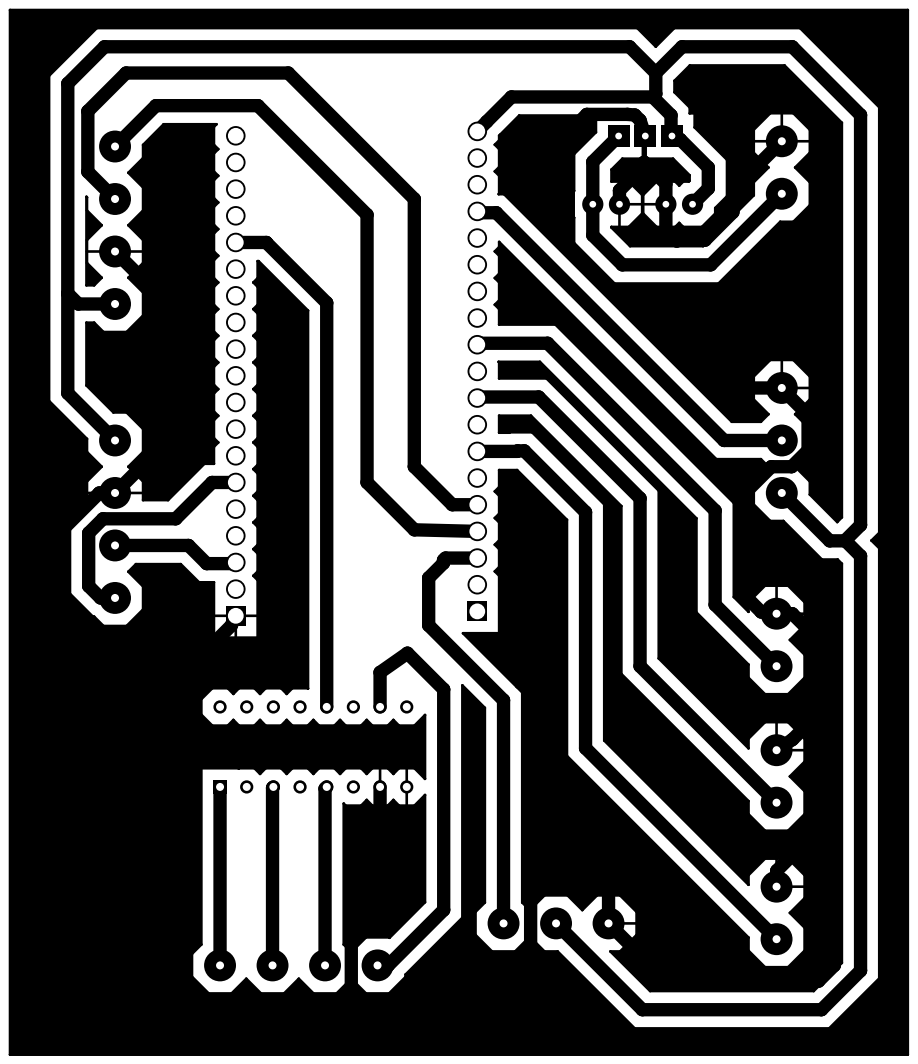
[picture p122: page 1]
