impatrq/green_house/Proteus/PCB horizontal.PDF

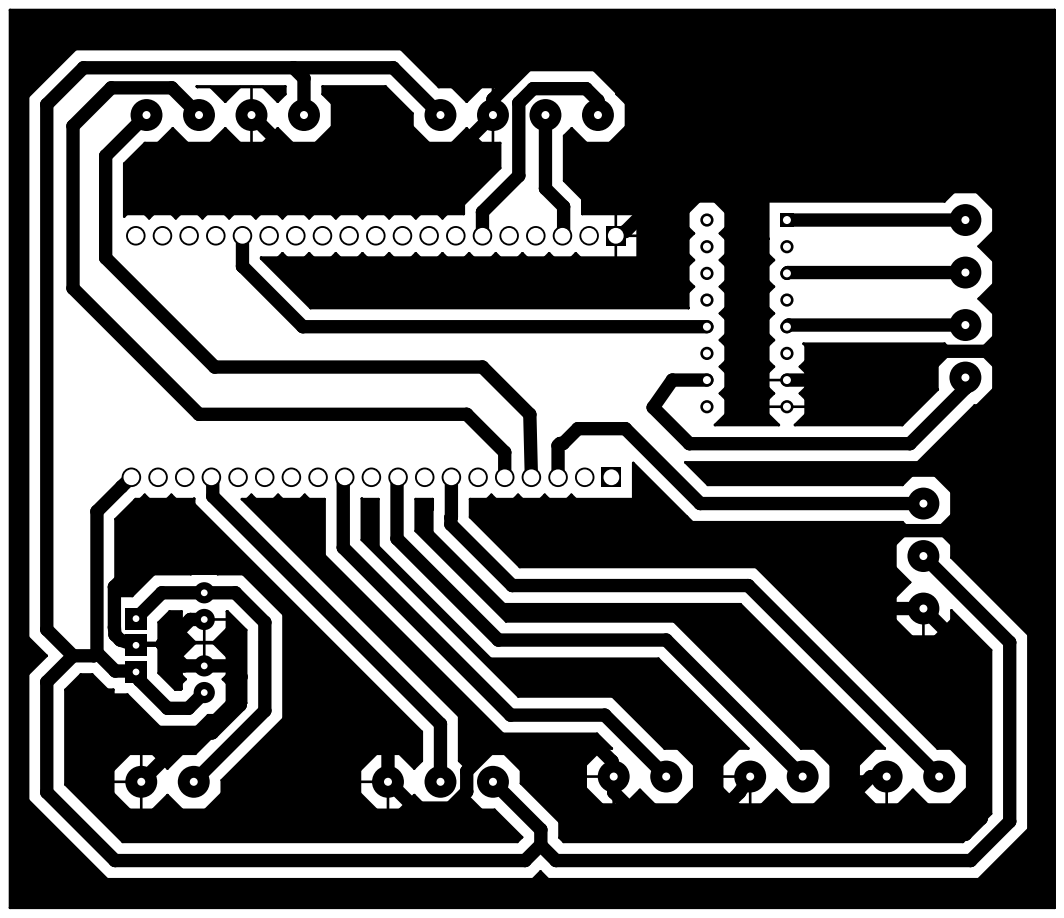
[picture p123: page 1]
