impatrq/green_house/Proteus/PCB vertical.PDF

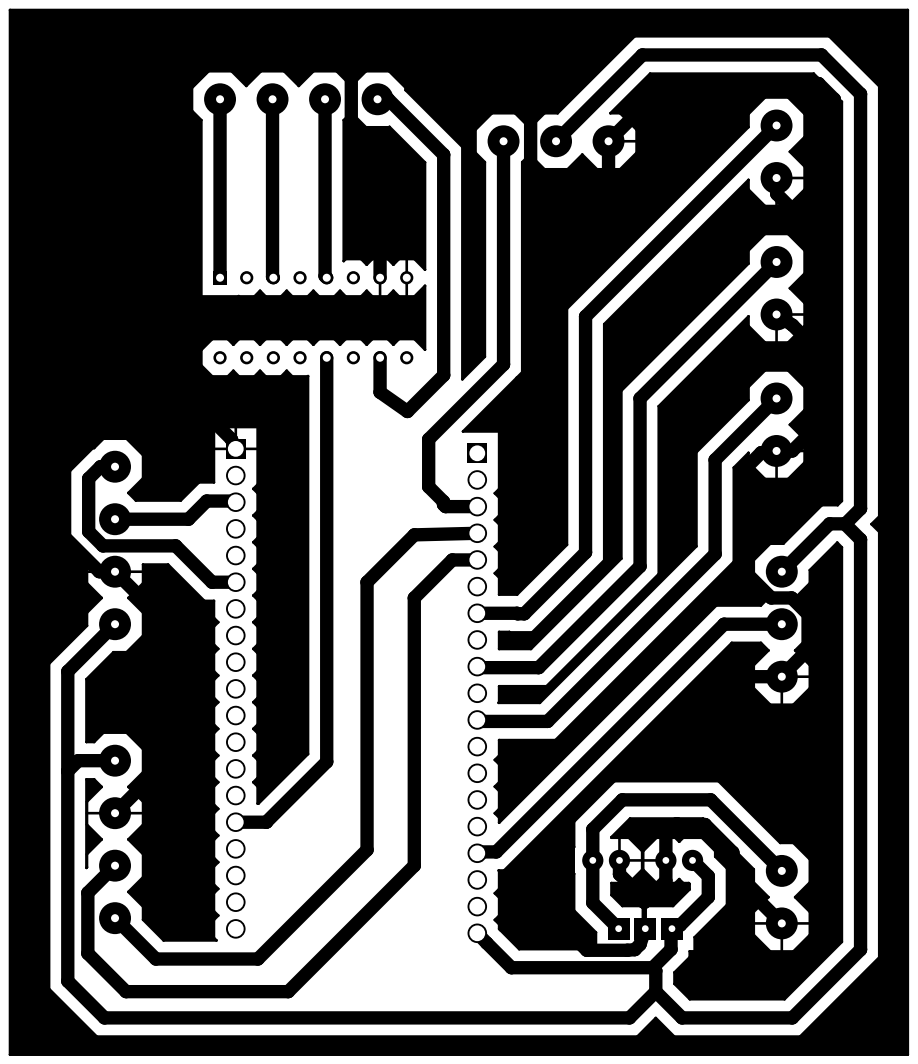
[picture p124: page 1]
